todbot/LinkM/c_host/linkm-lib.h

/**
 * linkm-lib --
 *
 * 2009, Tod E. Kurt, ThingM, http://thingm.com/
 *
 */

#ifndef __LINKM_LIB_H_INCLUDED__
#define __LINKM_LIB_H_INCLUDED__

#include <stdint.h>
#include "hiddata.h"

// NOTE: these values much be the same as those in
//       "linkm/firmware/usbconfig.h"           and
//       "linkm/bootloadHID/firmware/usbconfig.h"
//#define IDENT_VENDOR_NUM        0x16C0
//#define IDENT_PRODUCT_NUM       0x05DF
#define IDENT_VENDOR_NUM        0x20A0
#define IDENT_PRODUCT_NUM       0x4110
#define IDENT_VENDOR_STRING     "ThingM"
#define IDENT_PRODUCT_STRING    "LinkM"

// gotta be one more than the size, for the reportid
#define REPORT1_SIZE        17
//#define REPORT1_SIZE        16
#define START_BYTE          0xDA

// Command byte values for linkm_command()
enum {
    LINKM_CMD_NONE     = 0,      // no command, do not use
    // I2C commands
    LINKM_CMD_I2CTRANS = 1,      // i2c read & write (N args: addr + other)
    LINKM_CMD_I2CWRITE = 2,      // i2c write to dev (N args: addr + other)
    LINKM_CMD_I2CREAD  = 3,      // i2c read         (1 args: addr)
    LINKM_CMD_I2CSCAN  = 4,      // i2c bus scan     (2 args: start,end)
    LINKM_CMD_I2CCONN  = 5,      // i2c connect/disc (1 args: 1/0)
    LINKM_CMD_I2CINIT  = 6,      // i2c init         (0 args: )

    // linkm board commands
    LINKM_CMD_VERSIONGET = 100,  // return linkm version
    LINKM_CMD_STATLEDSET = 101,  // status LED set   (1 args: 1/0)
    LINKM_CMD_STATLEDGET = 102,  // status LED get   (0 args)
    LINKM_CMD_PLAYSET    = 103,  // set params of player state machine
    LINKM_CMD_PLAYGET    = 104,  // get params of  player state machine
    LINKM_CMD_EESAVE     = 105,  // save linkm state to EEPROM
    LINKM_CMD_EELOAD     = 106,  // load linkm state from EEPROM
    LINKM_CMD_GOBOOTLOAD = 107,  // trigger USB bootload
};

// Return values for linkm_command()
enum {
    LINKM_ERR_NONE     =   0,
    LINKM_ERR_BADSTART = 101,
    LINKM_ERR_BADARGS,
    LINKM_ERR_I2C,
    LINKM_ERR_I2CREAD,
    LINKM_ERR_NOTOPEN = 199,
};


extern int linkm_debug;


typedef struct {
    uint8_t duration;
    uint8_t cmd;
    uint8_t arg0;
    uint8_t arg1;
    uint8_t arg2;
} scriptline_t;


// public api
int linkm_open(usbDevice_t** dev);
void linkm_close(usbDevice_t* dev);
int linkm_command(usbDevice_t* dev,
                  int cmd,
                  int bytes_send,
                  int bytes_recv,
                  uint8_t* buf_send,
                  uint8_t* buf_recv);
char* linkm_error_msg(int errCode);

// utility
void hexdump(const char* intro, uint8_t* buffer, int len);
int  hexread(uint8_t* buffer, char* string, int buflen);
void linkm_sleep(uint32_t millis);
int parse_scriptlines( char* filename,  scriptline_t* lines );



#endif //__LINKM_LIB_H_INCLUDED__
