todbot/LinkM/c_host/hidsdi.h

/* Name: hidsdi.h
 * Author: Christian Starkjohann
 * Creation Date: 2006-02-02
 * Tabsize: 4
 * Copyright: (c) 2006-2008 by OBJECTIVE DEVELOPMENT Software GmbH
 * License: GNU GPL v2 (see License.txt), GNU GPL v3 or proprietary (CommercialLicense.txt)
 */

/*
General Description
This file is a replacement for hidsdi.h from the Windows DDK. It defines some
of the types and function prototypes of this header for our project. If you
have the Windows DDK version of this file or a version shipped with MinGW, use
that instead.
*/

#ifndef _HIDSDI_H
#define _HIDSDI_H

#include <pshpack4.h>

//#include <ddk/hidusage.h>
//#include <ddk/hidpi.h>

typedef struct{
    ULONG   Size;
    USHORT  VendorID;
    USHORT  ProductID;
    USHORT  VersionNumber;
}HIDD_ATTRIBUTES;

void __stdcall      HidD_GetHidGuid(OUT LPGUID hidGuid);

BOOLEAN __stdcall   HidD_GetAttributes(IN HANDLE device, OUT HIDD_ATTRIBUTES *attributes);

BOOLEAN __stdcall   HidD_GetManufacturerString(IN HANDLE device, OUT void *buffer, IN ULONG bufferLen);
BOOLEAN __stdcall   HidD_GetProductString(IN HANDLE device, OUT void *buffer, IN ULONG bufferLen);
BOOLEAN __stdcall   HidD_GetSerialNumberString(IN HANDLE device, OUT void *buffer, IN ULONG bufferLen);

BOOLEAN __stdcall   HidD_GetFeature(IN HANDLE device, OUT void *reportBuffer, IN ULONG bufferLen);
BOOLEAN __stdcall   HidD_SetFeature(IN HANDLE device, IN void *reportBuffer, IN ULONG bufferLen);

BOOLEAN __stdcall   HidD_GetNumInputBuffers(IN HANDLE device, OUT ULONG *numBuffers);
BOOLEAN __stdcall   HidD_SetNumInputBuffers(IN HANDLE device, OUT ULONG numBuffers);

#include <poppack.h>

#endif
