todbot/LinkM/tools/visual_studio/winddk.h

/*
 * winddk.h
 *
 * Windows Device Driver Kit
 *
 * This file is part of the w32api package.
 *
 * Contributors:
 *   Created by Casper S. Hornstrup <chorns@users.sourceforge.net>
 *
 * THIS SOFTWARE IS NOT COPYRIGHTED
 *
 * This source code is offered for use in the public domain. You may
 * use, modify or distribute it freely.
 *
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
 */

#ifndef __WINDDK_H
#define __WINDDK_H

#define _ANONYMOUS_UNION 
#define _ANONYMOUS_STRUCT

#if __GNUC__ >= 3
#pragma GCC system_header
#endif

#ifdef __cplusplus
extern "C" {
#endif

/*
** Definitions specific to this Device Driver Kit
*/
#define DDKAPI __stdcall
#define DDKFASTAPI __fastcall
#define DDKCDECLAPI __cdecl

#if defined(_NTOSKRNL_)
#ifndef NTOSAPI
#define NTOSAPI DECL_EXPORT
#endif
#define DECLARE_INTERNAL_OBJECT(x) typedef struct _##x; typedef struct _##x *P##x;
#define DECLARE_INTERNAL_OBJECT2(x,y) typedef struct _##x; typedef struct _##x *P##y;
#else
#ifndef NTOSAPI
#define NTOSAPI DECL_IMPORT
#endif
#define DECLARE_INTERNAL_OBJECT(x) struct _##x; typedef struct _##x *P##x;
#define DECLARE_INTERNAL_OBJECT2(x,y) struct _##x; typedef struct _##x *P##y;
#endif

/* Pseudo modifiers for parameters 
   We don't use these unnecessary defines in the w32api headers. Define
   them by default since that is what people expect, but allow users
   to avoid the pollution.  */
#ifndef _NO_W32_PSEUDO_MODIFIERS
#define IN
#define OUT
#define OPTIONAL
#define UNALLIGNED
#endif

#define CONST const
#define VOLATILE volatile

#define RESTRICTED_POINTER
#define POINTER_ALIGNMENT

#ifdef NONAMELESSUNION
# define _DDK_DUMMYUNION_MEMBER(name) DUMMYUNIONNAME.name
# define _DDK_DUMMYUNION_N_MEMBER(n, name) DUMMYUNIONNAME##n.name
#else
# define _DDK_DUMMYUNION_MEMBER(name) name
# define _DDK_DUMMYUNION_N_MEMBER(n, name) name
#endif

/*
** Forward declarations
*/

struct _IRP;
struct _MDL;
struct _KAPC;
struct _KDPC;
struct _KPCR;
struct _KPRCB;
struct _KTSS;
struct _FILE_OBJECT;
struct _DMA_ADAPTER;
struct _DEVICE_OBJECT;
struct _DRIVER_OBJECT;
struct _SECTION_OBJECT;
struct _IO_STATUS_BLOCK;
struct _DEVICE_DESCRIPTION;
struct _SCATTER_GATHER_LIST;

DECLARE_INTERNAL_OBJECT(ADAPTER_OBJECT)
DECLARE_INTERNAL_OBJECT(DMA_ADAPTER)
DECLARE_INTERNAL_OBJECT(IO_STATUS_BLOCK)
DECLARE_INTERNAL_OBJECT(SECTION_OBJECT)

#if 1
/* FIXME: Unknown definitions */
struct _SET_PARTITION_INFORMATION_EX;
typedef ULONG WAIT_TYPE;
typedef HANDLE TRACEHANDLE;
typedef PVOID PWMILIB_CONTEXT;
typedef PVOID PSYSCTL_IRP_DISPOSITION;
typedef ULONG LOGICAL;
#endif

/*
** Routines specific to this DDK
*/

#define TAG(_a, _b, _c, _d) (ULONG) \
	(((_a) << 0) + ((_b) << 8) + ((_c) << 16) + ((_d) << 24))

#ifdef __GNUC__
static __inline struct _KPCR * KeGetCurrentKPCR(
  VOID)
{
  ULONG Value;

  __asm__ __volatile__ (
#if (__GNUC__ >= 3)
    /* support -masm=intel */
    "mov{l} {%%fs:0x18, %0|%0, %%fs:0x18}\n\t"
#else
    "movl %%fs:0x18, %0\n\t"
#endif
     : "=r" (Value)
     : /* no inputs */
  );
  return (struct _KPCR *) Value;
}

#elif defined( __WATCOMC__ )

extern struct _KPCR * KeGetCurrentKPCR( void );
#pragma aux KeGetCurrentKPCR = \
  "mov eax, fs:[0x18]" \
  value [ eax ];

#endif

/*
** Simple structures
*/

typedef LONG KPRIORITY;
typedef UCHAR KIRQL, *PKIRQL;
typedef ULONG_PTR KSPIN_LOCK, *PKSPIN_LOCK;
typedef ULONG_PTR KAFFINITY, *PKAFFINITY;
typedef CCHAR KPROCESSOR_MODE;

typedef enum _MODE {
  KernelMode,
  UserMode,
  MaximumMode
} MODE;


/* Structures not exposed to drivers */
typedef struct _IO_TIMER *PIO_TIMER;
typedef struct _EPROCESS *PEPROCESS;
typedef struct _ETHREAD *PETHREAD;
typedef struct _KINTERRUPT *PKINTERRUPT;
typedef struct _OBJECT_TYPE *POBJECT_TYPE;
typedef struct _KTHREAD *PKTHREAD, *PRKTHREAD;
typedef struct _COMPRESSED_DATA_INFO *PCOMPRESSED_DATA_INFO;
typedef struct _HAL_DISPATCH_TABLE *PHAL_DISPATCH_TABLE;
typedef struct _HAL_PRIVATE_DISPATCH_TABLE *PHAL_PRIVATE_DISPATCH_TABLE;
typedef struct _DRIVE_LAYOUT_INFORMATION *PDRIVE_LAYOUT_INFORMATION;
typedef struct _DRIVE_LAYOUT_INFORMATION_EX *PDRIVE_LAYOUT_INFORMATION_EX;

/* Constants */
#define	MAXIMUM_PROCESSORS                32

#define MAXIMUM_WAIT_OBJECTS              64

#define METHOD_BUFFERED                   0
#define METHOD_IN_DIRECT                  1
#define METHOD_OUT_DIRECT                 2
#define METHOD_NEITHER                    3

#define LOW_PRIORITY                      0
#define LOW_REALTIME_PRIORITY             16
#define HIGH_PRIORITY                     31
#define MAXIMUM_PRIORITY                  32

#define FILE_SUPERSEDED                   0x00000000
#define FILE_OPENED                       0x00000001
#define FILE_CREATED                      0x00000002
#define FILE_OVERWRITTEN                  0x00000003
#define FILE_EXISTS                       0x00000004
#define FILE_DOES_NOT_EXIST               0x00000005

/* also in winnt.h */
//#define FILE_LIST_DIRECTORY               0x00000001
//#define FILE_READ_DATA                    0x00000001
//#define FILE_ADD_FILE                     0x00000002
//#define FILE_WRITE_DATA                   0x00000002
//#define FILE_ADD_SUBDIRECTORY             0x00000004
//#define FILE_APPEND_DATA                  0x00000004
//#define FILE_CREATE_PIPE_INSTANCE         0x00000004
//#define FILE_READ_EA                      0x00000008
//#define FILE_WRITE_EA                     0x00000010
//#define FILE_EXECUTE                      0x00000020
//#define FILE_TRAVERSE                     0x00000020
//#define FILE_DELETE_CHILD                 0x00000040
//#define FILE_READ_ATTRIBUTES              0x00000080
//#define FILE_WRITE_ATTRIBUTES             0x00000100

#define FILE_SHARE_READ                   0x00000001
#define FILE_SHARE_WRITE                  0x00000002
#define FILE_SHARE_DELETE                 0x00000004
#define FILE_SHARE_VALID_FLAGS            0x00000007

#define FILE_ATTRIBUTE_READONLY           0x00000001
#define FILE_ATTRIBUTE_HIDDEN             0x00000002
#define FILE_ATTRIBUTE_SYSTEM             0x00000004
#define FILE_ATTRIBUTE_DIRECTORY          0x00000010
#define FILE_ATTRIBUTE_ARCHIVE            0x00000020
#define FILE_ATTRIBUTE_DEVICE             0x00000040
#define FILE_ATTRIBUTE_NORMAL             0x00000080
#define FILE_ATTRIBUTE_TEMPORARY          0x00000100
#define FILE_ATTRIBUTE_SPARSE_FILE        0x00000200
#define FILE_ATTRIBUTE_REPARSE_POINT      0x00000400
#define FILE_ATTRIBUTE_COMPRESSED         0x00000800
#define FILE_ATTRIBUTE_OFFLINE            0x00001000
#define FILE_ATTRIBUTE_NOT_CONTENT_INDEXED 0x00002000
#define FILE_ATTRIBUTE_ENCRYPTED          0x00004000

#define FILE_ATTRIBUTE_VALID_FLAGS        0x00007fb7
#define FILE_ATTRIBUTE_VALID_SET_FLAGS    0x000031a7

#define FILE_COPY_STRUCTURED_STORAGE      0x00000041
#define FILE_STRUCTURED_STORAGE           0x00000441

#define FILE_VALID_OPTION_FLAGS           0x00ffffff
#define FILE_VALID_PIPE_OPTION_FLAGS      0x00000032
#define FILE_VALID_MAILSLOT_OPTION_FLAGS  0x00000032
#define FILE_VALID_SET_FLAGS              0x00000036

#define FILE_SUPERSEDE                    0x00000000
#define FILE_OPEN                         0x00000001
#define FILE_CREATE                       0x00000002
#define FILE_OPEN_IF                      0x00000003
#define FILE_OVERWRITE                    0x00000004
#define FILE_OVERWRITE_IF                 0x00000005
#define FILE_MAXIMUM_DISPOSITION          0x00000005

#define FILE_DIRECTORY_FILE               0x00000001
#define FILE_WRITE_THROUGH                0x00000002
#define FILE_SEQUENTIAL_ONLY              0x00000004
#define FILE_NO_INTERMEDIATE_BUFFERING    0x00000008
#define FILE_SYNCHRONOUS_IO_ALERT         0x00000010
#define FILE_SYNCHRONOUS_IO_NONALERT      0x00000020
#define FILE_NON_DIRECTORY_FILE           0x00000040
#define FILE_CREATE_TREE_CONNECTION       0x00000080
#define FILE_COMPLETE_IF_OPLOCKED         0x00000100
#define FILE_NO_EA_KNOWLEDGE              0x00000200
#define FILE_OPEN_FOR_RECOVERY            0x00000400
#define FILE_RANDOM_ACCESS                0x00000800
#define FILE_DELETE_ON_CLOSE              0x00001000
#define FILE_OPEN_BY_FILE_ID              0x00002000
#define FILE_OPEN_FOR_BACKUP_INTENT       0x00004000
#define FILE_NO_COMPRESSION               0x00008000
#define FILE_RESERVE_OPFILTER             0x00100000
#define FILE_OPEN_REPARSE_POINT           0x00200000
#define FILE_OPEN_NO_RECALL               0x00400000
#define FILE_OPEN_FOR_FREE_SPACE_QUERY    0x00800000

//#define FILE_ANY_ACCESS                   0x00000000
//#define FILE_SPECIAL_ACCESS               FILE_ANY_ACCESS
//#define FILE_READ_ACCESS                  0x00000001
//#define FILE_WRITE_ACCESS                 0x00000002

#define FILE_ALL_ACCESS \
  (STANDARD_RIGHTS_REQUIRED | \
   SYNCHRONIZE | \
   0x1FF)

#define FILE_GENERIC_EXECUTE \
  (STANDARD_RIGHTS_EXECUTE | \
   FILE_READ_ATTRIBUTES | \
   FILE_EXECUTE | \
   SYNCHRONIZE)

#define FILE_GENERIC_READ \
  (STANDARD_RIGHTS_READ | \
   FILE_READ_DATA | \
   FILE_READ_ATTRIBUTES | \
   FILE_READ_EA | \
   SYNCHRONIZE)

#define FILE_GENERIC_WRITE \
  (STANDARD_RIGHTS_WRITE | \
   FILE_WRITE_DATA | \
   FILE_WRITE_ATTRIBUTES | \
   FILE_WRITE_EA | \
   FILE_APPEND_DATA | \
   SYNCHRONIZE)
/* end winnt.h */

#define DIRECTORY_QUERY (0x0001)
#define DIRECTORY_TRAVERSE (0x0002)
#define DIRECTORY_CREATE_OBJECT (0x0004)
#define DIRECTORY_CREATE_SUBDIRECTORY (0x0008)
#define DIRECTORY_ALL_ACCESS (STANDARD_RIGHTS_REQUIRED | 0xF)
  
/* Exported object types */
extern NTOSAPI POBJECT_TYPE ExDesktopObjectType;
extern NTOSAPI POBJECT_TYPE ExEventObjectType;
extern NTOSAPI POBJECT_TYPE ExSemaphoreObjectType;
extern NTOSAPI POBJECT_TYPE ExWindowStationObjectType;
extern NTOSAPI POBJECT_TYPE IoAdapterObjectType;
extern NTOSAPI ULONG IoDeviceHandlerObjectSize;
extern NTOSAPI POBJECT_TYPE IoDeviceHandlerObjectType;
extern NTOSAPI POBJECT_TYPE IoDeviceObjectType;
extern NTOSAPI POBJECT_TYPE IoDriverObjectType;
extern NTOSAPI POBJECT_TYPE IoFileObjectType;
extern NTOSAPI POBJECT_TYPE LpcPortObjectType;
extern NTOSAPI POBJECT_TYPE MmSectionObjectType;
extern NTOSAPI POBJECT_TYPE SeTokenObjectType;

extern NTOSAPI CCHAR KeNumberProcessors;
extern NTOSAPI PHAL_DISPATCH_TABLE HalDispatchTable;
extern NTOSAPI PHAL_PRIVATE_DISPATCH_TABLE HalPrivateDispatchTable;


/*
** IRP function codes
*/

#define IRP_MJ_CREATE                     0x00
#define IRP_MJ_CREATE_NAMED_PIPE          0x01
#define IRP_MJ_CLOSE                      0x02
#define IRP_MJ_READ                       0x03
#define IRP_MJ_WRITE                      0x04
#define IRP_MJ_QUERY_INFORMATION          0x05
#define IRP_MJ_SET_INFORMATION            0x06
#define IRP_MJ_QUERY_EA                   0x07
#define IRP_MJ_SET_EA                     0x08
#define IRP_MJ_FLUSH_BUFFERS              0x09
#define IRP_MJ_QUERY_VOLUME_INFORMATION   0x0a
#define IRP_MJ_SET_VOLUME_INFORMATION     0x0b
#define IRP_MJ_DIRECTORY_CONTROL          0x0c
#define IRP_MJ_FILE_SYSTEM_CONTROL        0x0d
#define IRP_MJ_DEVICE_CONTROL             0x0e
#define IRP_MJ_INTERNAL_DEVICE_CONTROL    0x0f
#define IRP_MJ_SCSI                       0x0f
#define IRP_MJ_SHUTDOWN                   0x10
#define IRP_MJ_LOCK_CONTROL               0x11
#define IRP_MJ_CLEANUP                    0x12
#define IRP_MJ_CREATE_MAILSLOT            0x13
#define IRP_MJ_QUERY_SECURITY             0x14
#define IRP_MJ_SET_SECURITY               0x15
#define IRP_MJ_POWER                      0x16
#define IRP_MJ_SYSTEM_CONTROL             0x17
#define IRP_MJ_DEVICE_CHANGE              0x18
#define IRP_MJ_QUERY_QUOTA                0x19
#define IRP_MJ_SET_QUOTA                  0x1a
#define IRP_MJ_PNP                        0x1b
#define IRP_MJ_PNP_POWER                  0x1b
#define IRP_MJ_MAXIMUM_FUNCTION           0x1b

#define IRP_MN_QUERY_DIRECTORY            0x01
#define IRP_MN_NOTIFY_CHANGE_DIRECTORY    0x02

#define IRP_MN_USER_FS_REQUEST            0x00
#define IRP_MN_MOUNT_VOLUME               0x01
#define IRP_MN_VERIFY_VOLUME              0x02
#define IRP_MN_LOAD_FILE_SYSTEM           0x03
#define IRP_MN_TRACK_LINK                 0x04
#define IRP_MN_KERNEL_CALL                0x04

#define IRP_MN_LOCK                       0x01
#define IRP_MN_UNLOCK_SINGLE              0x02
#define IRP_MN_UNLOCK_ALL                 0x03
#define IRP_MN_UNLOCK_ALL_BY_KEY          0x04

#define IRP_MN_NORMAL                     0x00
#define IRP_MN_DPC                        0x01
#define IRP_MN_MDL                        0x02
#define IRP_MN_COMPLETE                   0x04
#define IRP_MN_COMPRESSED                 0x08

#define IRP_MN_MDL_DPC                    (IRP_MN_MDL | IRP_MN_DPC)
#define IRP_MN_COMPLETE_MDL               (IRP_MN_COMPLETE | IRP_MN_MDL)
#define IRP_MN_COMPLETE_MDL_DPC           (IRP_MN_COMPLETE_MDL | IRP_MN_DPC)

#define IRP_MN_SCSI_CLASS                 0x01

#define IRP_MN_START_DEVICE               0x00
#define IRP_MN_QUERY_REMOVE_DEVICE        0x01
#define IRP_MN_REMOVE_DEVICE              0x02
#define IRP_MN_CANCEL_REMOVE_DEVICE       0x03
#define IRP_MN_STOP_DEVICE                0x04
#define IRP_MN_QUERY_STOP_DEVICE          0x05
#define IRP_MN_CANCEL_STOP_DEVICE         0x06

#define IRP_MN_QUERY_DEVICE_RELATIONS       0x07
#define IRP_MN_QUERY_INTERFACE              0x08
#define IRP_MN_QUERY_CAPABILITIES           0x09
#define IRP_MN_QUERY_RESOURCES              0x0A
#define IRP_MN_QUERY_RESOURCE_REQUIREMENTS  0x0B
#define IRP_MN_QUERY_DEVICE_TEXT            0x0C
#define IRP_MN_FILTER_RESOURCE_REQUIREMENTS 0x0D

#define IRP_MN_READ_CONFIG                  0x0F
#define IRP_MN_WRITE_CONFIG                 0x10
#define IRP_MN_EJECT                        0x11
#define IRP_MN_SET_LOCK                     0x12
#define IRP_MN_QUERY_ID                     0x13
#define IRP_MN_QUERY_PNP_DEVICE_STATE       0x14
#define IRP_MN_QUERY_BUS_INFORMATION        0x15
#define IRP_MN_DEVICE_USAGE_NOTIFICATION    0x16
#define IRP_MN_SURPRISE_REMOVAL             0x17
#define IRP_MN_QUERY_LEGACY_BUS_INFORMATION 0x18

#define IRP_MN_WAIT_WAKE                  0x00
#define IRP_MN_POWER_SEQUENCE             0x01
#define IRP_MN_SET_POWER                  0x02
#define IRP_MN_QUERY_POWER                0x03

#define IRP_MN_QUERY_ALL_DATA             0x00
#define IRP_MN_QUERY_SINGLE_INSTANCE      0x01
#define IRP_MN_CHANGE_SINGLE_INSTANCE     0x02
#define IRP_MN_CHANGE_SINGLE_ITEM         0x03
#define IRP_MN_ENABLE_EVENTS              0x04
#define IRP_MN_DISABLE_EVENTS             0x05
#define IRP_MN_ENABLE_COLLECTION          0x06
#define IRP_MN_DISABLE_COLLECTION         0x07
#define IRP_MN_REGINFO                    0x08
#define IRP_MN_EXECUTE_METHOD             0x09

#define IRP_MN_REGINFO_EX                 0x0b

typedef enum _IO_ALLOCATION_ACTION {
  KeepObject = 1,
  DeallocateObject,
  DeallocateObjectKeepRegisters
} IO_ALLOCATION_ACTION, *PIO_ALLOCATION_ACTION;

typedef IO_ALLOCATION_ACTION
(DDKAPI *PDRIVER_CONTROL)(
  /*IN*/ struct _DEVICE_OBJECT  *DeviceObject,
  /*IN*/ struct _IRP  *Irp,
  /*IN*/ PVOID  MapRegisterBase,
  /*IN*/ PVOID  Context);

typedef VOID
(DDKAPI *PDRIVER_LIST_CONTROL)(
  /*IN*/ struct _DEVICE_OBJECT  *DeviceObject,
  /*IN*/ struct _IRP  *Irp,
  /*IN*/ struct _SCATTER_GATHER_LIST  *ScatterGather,
  /*IN*/ PVOID  Context);

typedef NTSTATUS
(DDKAPI *PDRIVER_ADD_DEVICE)(
  /*IN*/ struct _DRIVER_OBJECT  *DriverObject,
  /*IN*/ struct _DEVICE_OBJECT  *PhysicalDeviceObject);

typedef NTSTATUS
(DDKAPI *PIO_COMPLETION_ROUTINE)(
  /*IN*/ struct _DEVICE_OBJECT  *DeviceObject,
  /*IN*/ struct _IRP  *Irp,
  /*IN*/ PVOID  Context);

typedef VOID
(DDKAPI *PDRIVER_CANCEL)(
  /*IN*/ struct _DEVICE_OBJECT  *DeviceObject,
  /*IN*/ struct _IRP  *Irp);

typedef VOID
(DDKAPI *PKDEFERRED_ROUTINE)(
  /*IN*/ struct _KDPC  *Dpc,
  /*IN*/ PVOID  DeferredContext,
  /*IN*/ PVOID  SystemArgument1,
  /*IN*/ PVOID  SystemArgument2);

typedef NTSTATUS
(DDKAPI *PDRIVER_DISPATCH)(
  /*IN*/ struct _DEVICE_OBJECT  *DeviceObject,
  /*IN*/ struct _IRP  *Irp);

typedef VOID
(DDKAPI *PIO_DPC_ROUTINE)(
  /*IN*/ struct _KDPC  *Dpc,
  /*IN*/ struct _DEVICE_OBJECT  *DeviceObject,
  /*IN*/ struct _IRP  *Irp,
  /*IN*/ PVOID  Context);

typedef NTSTATUS
(DDKAPI *PMM_DLL_INITIALIZE)(
  /*IN*/ PUNICODE_STRING  RegistryPath);

typedef NTSTATUS
(DDKAPI *PMM_DLL_UNLOAD)(
  VOID);

typedef NTSTATUS
(DDKAPI *PDRIVER_ENTRY)( 
  /*IN*/ struct _DRIVER_OBJECT  *DriverObject, 
  /*IN*/ PUNICODE_STRING  RegistryPath); 

typedef NTSTATUS
(DDKAPI *PDRIVER_INITIALIZE)(
  /*IN*/ struct _DRIVER_OBJECT  *DriverObject, 
  /*IN*/ PUNICODE_STRING  RegistryPath);

typedef BOOLEAN
(DDKAPI *PKSERVICE_ROUTINE)(
  /*IN*/ struct _KINTERRUPT  *Interrupt,
  /*IN*/ PVOID  ServiceContext);

typedef VOID
(DDKAPI *PIO_TIMER_ROUTINE)(
  /*IN*/ struct _DEVICE_OBJECT  *DeviceObject,
  /*IN*/ PVOID  Context);

typedef VOID
(DDKAPI *PDRIVER_REINITIALIZE)( 
  /*IN*/ struct _DRIVER_OBJECT  *DriverObject, 
  /*IN*/ PVOID  Context, 
  /*IN*/ ULONG  Count); 

typedef NTSTATUS
(DDKAPI *PDRIVER_STARTIO)(
  /*IN*/ struct _DEVICE_OBJECT  *DeviceObject,
  /*IN*/ struct _IRP  *Irp);

typedef BOOLEAN
(DDKAPI *PKSYNCHRONIZE_ROUTINE)(
  /*IN*/ PVOID  SynchronizeContext);

typedef VOID
(DDKAPI *PDRIVER_UNLOAD)( 
  /*IN*/ struct _DRIVER_OBJECT  *DriverObject); 



/*
** Plug and Play structures
*/

typedef VOID  (DDKAPI *PINTERFACE_REFERENCE)(PVOID  Context);

typedef VOID 
(DDKAPI *PINTERFACE_DEREFERENCE)(
  PVOID Context);

typedef BOOLEAN 
(DDKAPI *PTRANSLATE_BUS_ADDRESS)(
  /*IN*/ PVOID  Context,
  /*IN*/ PHYSICAL_ADDRESS  BusAddress,
  /*IN*/ ULONG  Length,
  /*IN OUT*/ PULONG  AddressSpace,
  /*OUT*/ PPHYSICAL_ADDRESS  TranslatedAddress);

typedef struct _DMA_ADAPTER* 
(DDKAPI *PGET_DMA_ADAPTER)(
  /*IN*/ PVOID  Context,
  /*IN*/ struct _DEVICE_DESCRIPTION  *DeviceDescriptor,
  /*OUT*/ PULONG  NumberOfMapRegisters);

typedef ULONG 
(DDKAPI *PGET_SET_DEVICE_DATA)(
  /*IN*/ PVOID  Context,
  /*IN*/ ULONG  DataType,
  /*IN*/ PVOID  Buffer,
  /*IN*/ ULONG  Offset,
  /*IN*/ ULONG  Length);

typedef union _POWER_STATE {
  SYSTEM_POWER_STATE  SystemState;
  DEVICE_POWER_STATE  DeviceState;
} POWER_STATE, *PPOWER_STATE;

typedef enum _POWER_STATE_TYPE {
  SystemPowerState,
  DevicePowerState
} POWER_STATE_TYPE, *PPOWER_STATE_TYPE;

typedef struct _BUS_INTERFACE_STANDARD {
  USHORT  Size;
  USHORT  Version;
  PVOID  Context;
  PINTERFACE_REFERENCE  InterfaceReference;
  PINTERFACE_DEREFERENCE  InterfaceDereference;
  PTRANSLATE_BUS_ADDRESS  TranslateBusAddress;
  PGET_DMA_ADAPTER  GetDmaAdapter;
  PGET_SET_DEVICE_DATA  SetBusData;
  PGET_SET_DEVICE_DATA  GetBusData;
} BUS_INTERFACE_STANDARD, *PBUS_INTERFACE_STANDARD;

typedef struct _DEVICE_CAPABILITIES {
  USHORT  Size;
  USHORT  Version;
  ULONG  DeviceD1 : 1;
  ULONG  DeviceD2 : 1;
  ULONG  LockSupported : 1;
  ULONG  EjectSupported : 1;
  ULONG  Removable : 1;
  ULONG  DockDevice : 1;
  ULONG  UniqueID : 1;
  ULONG  SilentInstall : 1;
  ULONG  RawDeviceOK : 1;
  ULONG  SurpriseRemovalOK : 1;
  ULONG  WakeFromD0 : 1;
  ULONG  WakeFromD1 : 1;
  ULONG  WakeFromD2 : 1;
  ULONG  WakeFromD3 : 1;
  ULONG  HardwareDisabled : 1;
  ULONG  NonDynamic : 1;
  ULONG  WarmEjectSupported : 1;
  ULONG  NoDisplayInUI : 1;
  ULONG  Reserved : 14;
  ULONG  Address;
  ULONG  UINumber;
  DEVICE_POWER_STATE  DeviceState[PowerSystemMaximum];
  SYSTEM_POWER_STATE  SystemWake;
  DEVICE_POWER_STATE  DeviceWake;
  ULONG  D1Latency;
  ULONG  D2Latency;
  ULONG  D3Latency;
} DEVICE_CAPABILITIES, *PDEVICE_CAPABILITIES;

typedef struct _DEVICE_INTERFACE_CHANGE_NOTIFICATION {
  USHORT  Version;
  USHORT  Size;
  GUID  Event;
  GUID  InterfaceClassGuid;
  PUNICODE_STRING  SymbolicLinkName;
} DEVICE_INTERFACE_CHANGE_NOTIFICATION, *PDEVICE_INTERFACE_CHANGE_NOTIFICATION;

typedef struct _HWPROFILE_CHANGE_NOTIFICATION {
  USHORT  Version;
  USHORT  Size;
  GUID  Event;
} HWPROFILE_CHANGE_NOTIFICATION, *PHWPROFILE_CHANGE_NOTIFICATION;

#undef INTERFACE

typedef struct _INTERFACE {
  USHORT  Size;
  USHORT  Version;
  PVOID  Context;
  PINTERFACE_REFERENCE  InterfaceReference;
  PINTERFACE_DEREFERENCE  InterfaceDereference;
} INTERFACE, *PINTERFACE; 

typedef struct _PLUGPLAY_NOTIFICATION_HEADER {
  USHORT  Version; 
  USHORT  Size; 
  GUID  Event;
} PLUGPLAY_NOTIFICATION_HEADER, *PPLUGPLAY_NOTIFICATION_HEADER;

typedef ULONG PNP_DEVICE_STATE, *PPNP_DEVICE_STATE;

/* PNP_DEVICE_STATE */

#define PNP_DEVICE_DISABLED                      0x00000001
#define PNP_DEVICE_DONT_DISPLAY_IN_UI            0x00000002
#define PNP_DEVICE_FAILED                        0x00000004
#define PNP_DEVICE_REMOVED                       0x00000008
#define PNP_DEVICE_RESOURCE_REQUIREMENTS_CHANGED 0x00000010
#define PNP_DEVICE_NOT_DISABLEABLE               0x00000020

typedef struct _TARGET_DEVICE_CUSTOM_NOTIFICATION {
  USHORT  Version;
  USHORT  Size;
  GUID  Event;
  struct _FILE_OBJECT  *FileObject;
  LONG  NameBufferOffset;
  UCHAR  CustomDataBuffer[1];
} TARGET_DEVICE_CUSTOM_NOTIFICATION, *PTARGET_DEVICE_CUSTOM_NOTIFICATION;

typedef struct _TARGET_DEVICE_REMOVAL_NOTIFICATION {
  USHORT  Version;
  USHORT  Size;
  GUID  Event;
  struct _FILE_OBJECT  *FileObject;
} TARGET_DEVICE_REMOVAL_NOTIFICATION, *PTARGET_DEVICE_REMOVAL_NOTIFICATION;

typedef enum _BUS_QUERY_ID_TYPE {
  BusQueryDeviceID,
  BusQueryHardwareIDs,
  BusQueryCompatibleIDs,
  BusQueryInstanceID,
  BusQueryDeviceSerialNumber
} BUS_QUERY_ID_TYPE, *PBUS_QUERY_ID_TYPE;

typedef enum _DEVICE_TEXT_TYPE {
  DeviceTextDescription,
  DeviceTextLocationInformation
} DEVICE_TEXT_TYPE, *PDEVICE_TEXT_TYPE;

typedef enum _DEVICE_USAGE_NOTIFICATION_TYPE {
  DeviceUsageTypeUndefined,
  DeviceUsageTypePaging,
  DeviceUsageTypeHibernation,
  DeviceUsageTypeDumpFile
} DEVICE_USAGE_NOTIFICATION_TYPE;

typedef struct _POWER_SEQUENCE {
  ULONG  SequenceD1;
  ULONG  SequenceD2;
  ULONG  SequenceD3;
} POWER_SEQUENCE, *PPOWER_SEQUENCE;

typedef enum {
  DevicePropertyDeviceDescription,
  DevicePropertyHardwareID,
  DevicePropertyCompatibleIDs,
  DevicePropertyBootConfiguration,
  DevicePropertyBootConfigurationTranslated,
  DevicePropertyClassName,
  DevicePropertyClassGuid,
  DevicePropertyDriverKeyName,
  DevicePropertyManufacturer,
  DevicePropertyFriendlyName,
  DevicePropertyLocationInformation,
  DevicePropertyPhysicalDeviceObjectName,
  DevicePropertyBusTypeGuid,
  DevicePropertyLegacyBusType,
  DevicePropertyBusNumber,
  DevicePropertyEnumeratorName,
  DevicePropertyAddress,
  DevicePropertyUINumber,
  DevicePropertyInstallState,
  DevicePropertyRemovalPolicy
} DEVICE_REGISTRY_PROPERTY;

typedef enum _IO_NOTIFICATION_EVENT_CATEGORY {
  EventCategoryReserved,
  EventCategoryHardwareProfileChange,
  EventCategoryDeviceInterfaceChange,
  EventCategoryTargetDeviceChange
} IO_NOTIFICATION_EVENT_CATEGORY;

#define PNPNOTIFY_DEVICE_INTERFACE_INCLUDE_EXISTING_INTERFACES    0x00000001

typedef NTSTATUS 
(DDKAPI *PDRIVER_NOTIFICATION_CALLBACK_ROUTINE)(
  /*IN*/ PVOID NotificationStructure,
  /*IN*/ PVOID Context);

typedef VOID 
(DDKAPI *PDEVICE_CHANGE_COMPLETE_CALLBACK)(
  /*IN*/ PVOID Context);



/*
** System structures
*/

#define SYMBOLIC_LINK_QUERY               0x0001
#define SYMBOLIC_LINK_ALL_ACCESS          (STANDARD_RIGHTS_REQUIRED | 0x1)

/* also in winnt,h */
#define DUPLICATE_CLOSE_SOURCE            0x00000001
#define DUPLICATE_SAME_ACCESS             0x00000002
#define DUPLICATE_SAME_ATTRIBUTES         0x00000004
/* end winnt.h */

typedef struct _OBJECT_NAME_INFORMATION {               
  UNICODE_STRING  Name;                                
} OBJECT_NAME_INFORMATION, *POBJECT_NAME_INFORMATION;   

typedef VOID 
(DDKAPI *PIO_APC_ROUTINE)(
  /*IN*/ PVOID ApcContext,
  /*IN*/ PIO_STATUS_BLOCK IoStatusBlock,
  /*IN*/ ULONG Reserved);

typedef struct _IO_STATUS_BLOCK {
  _ANONYMOUS_UNION union {
    NTSTATUS  Status;
    PVOID  Pointer;
  } DUMMYUNIONNAME;
  ULONG_PTR  Information;
} IO_STATUS_BLOCK;

typedef VOID 
(DDKAPI *PKNORMAL_ROUTINE)(
  /*IN*/ PVOID  NormalContext,
  /*IN*/ PVOID  SystemArgument1,
  /*IN*/ PVOID  SystemArgument2);

typedef VOID 
(DDKAPI *PKKERNEL_ROUTINE)(
  /*IN*/ struct _KAPC  *Apc,
  /*IN OUT*/ PKNORMAL_ROUTINE  *NormalRoutine,
  /*IN OUT*/ PVOID  *NormalContext,
  /*IN OUT*/ PVOID  *SystemArgument1,
  /*IN OUT*/ PVOID  *SystemArgument2);

typedef VOID 
(DDKAPI *PKRUNDOWN_ROUTINE)(
  /*IN*/ struct _KAPC  *Apc);

typedef BOOLEAN 
(DDKAPI *PKTRANSFER_ROUTINE)(
  VOID);

typedef struct _KAPC {
  CSHORT  Type;
  CSHORT  Size;
  ULONG  Spare0;
  struct _KTHREAD  *Thread;
  LIST_ENTRY  ApcListEntry;
  PKKERNEL_ROUTINE  KernelRoutine;
  PKRUNDOWN_ROUTINE  RundownRoutine;
  PKNORMAL_ROUTINE  NormalRoutine;
  PVOID  NormalContext;
  PVOID  SystemArgument1;
  PVOID  SystemArgument2;
  CCHAR  ApcStateIndex;
  KPROCESSOR_MODE  ApcMode;
  BOOLEAN  Inserted;
} KAPC, *PKAPC, *RESTRICTED_POINTER PRKAPC;

typedef struct _KDEVICE_QUEUE {
  CSHORT  Type;
  CSHORT  Size;
  LIST_ENTRY  DeviceListHead;
  KSPIN_LOCK  Lock;
  BOOLEAN  Busy;
} KDEVICE_QUEUE, *PKDEVICE_QUEUE, *RESTRICTED_POINTER PRKDEVICE_QUEUE;

typedef struct _KDEVICE_QUEUE_ENTRY {
  LIST_ENTRY  DeviceListEntry;
  ULONG  SortKey;
  BOOLEAN  Inserted;
} KDEVICE_QUEUE_ENTRY, *PKDEVICE_QUEUE_ENTRY,
*RESTRICTED_POINTER PRKDEVICE_QUEUE_ENTRY;

#define LOCK_QUEUE_WAIT                   1
#define LOCK_QUEUE_OWNER                  2

typedef enum _KSPIN_LOCK_QUEUE_NUMBER {
  LockQueueDispatcherLock,
  LockQueueContextSwapLock,
  LockQueuePfnLock,
  LockQueueSystemSpaceLock,
  LockQueueVacbLock,
  LockQueueMasterLock,
  LockQueueNonPagedPoolLock,
  LockQueueIoCancelLock,
  LockQueueWorkQueueLock,
  LockQueueIoVpbLock,
  LockQueueIoDatabaseLock,
  LockQueueIoCompletionLock,
  LockQueueNtfsStructLock,
  LockQueueAfdWorkQueueLock,
  LockQueueBcbLock,
  LockQueueMaximumLock
} KSPIN_LOCK_QUEUE_NUMBER, *PKSPIN_LOCK_QUEUE_NUMBER;

typedef struct _KSPIN_LOCK_QUEUE {
  struct _KSPIN_LOCK_QUEUE  *VOLATILE Next;
  PKSPIN_LOCK VOLATILE  Lock;
} KSPIN_LOCK_QUEUE, *PKSPIN_LOCK_QUEUE;

typedef struct _KLOCK_QUEUE_HANDLE {
  KSPIN_LOCK_QUEUE  LockQueue;
  KIRQL  OldIrql;
} KLOCK_QUEUE_HANDLE, *PKLOCK_QUEUE_HANDLE;

typedef struct _KDPC {
  CSHORT  Type;
  UCHAR  Number;
  UCHAR  Importance;
  LIST_ENTRY  DpcListEntry;
  PKDEFERRED_ROUTINE  DeferredRoutine;
  PVOID  DeferredContext;
  PVOID  SystemArgument1;
  PVOID  SystemArgument2;
  PULONG_PTR  Lock;
} KDPC, *PKDPC, *RESTRICTED_POINTER PRKDPC;

typedef struct _WAIT_CONTEXT_BLOCK {
  KDEVICE_QUEUE_ENTRY  WaitQueueEntry;
  struct _DRIVER_CONTROL  *DeviceRoutine;
  PVOID  DeviceContext;
  ULONG  NumberOfMapRegisters;
  PVOID  DeviceObject;
  PVOID  CurrentIrp;
  PKDPC  BufferChainingDpc;
} WAIT_CONTEXT_BLOCK, *PWAIT_CONTEXT_BLOCK;

typedef struct _DISPATCHER_HEADER {
  UCHAR  Type;
  UCHAR  Absolute;
  UCHAR  Size;
  UCHAR  Inserted;
  LONG  SignalState;
  LIST_ENTRY  WaitListHead;
} DISPATCHER_HEADER, *PDISPATCHER_HEADER;

typedef struct _KEVENT {
  DISPATCHER_HEADER  Header;
} KEVENT, *PKEVENT, *RESTRICTED_POINTER PRKEVENT;

typedef struct _KSEMAPHORE {
    DISPATCHER_HEADER Header;
    LONG Limit;
} KSEMAPHORE, *PKSEMAPHORE, *RESTRICTED_POINTER PRKSEMAPHORE;

typedef struct _FAST_MUTEX {
  LONG  Count;
  struct _KTHREAD  *Owner;
  ULONG  Contention;
  KEVENT  Event;
  ULONG  OldIrql;
} FAST_MUTEX, *PFAST_MUTEX;

typedef struct _KTIMER {
  DISPATCHER_HEADER  Header;
  ULARGE_INTEGER  DueTime;
  LIST_ENTRY  TimerListEntry;
  struct _KDPC  *Dpc;
  LONG  Period;
} KTIMER, *PKTIMER, *RESTRICTED_POINTER PRKTIMER;

typedef struct _KMUTANT {
  DISPATCHER_HEADER  Header;
  LIST_ENTRY  MutantListEntry;
  struct _KTHREAD  *RESTRICTED_POINTER OwnerThread;
  BOOLEAN  Abandoned;
  UCHAR  ApcDisable;
} KMUTANT, *PKMUTANT, *RESTRICTED_POINTER PRKMUTANT, KMUTEX, *PKMUTEX, *RESTRICTED_POINTER PRKMUTEX;

typedef enum _TIMER_TYPE {
  NotificationTimer,
  SynchronizationTimer
} TIMER_TYPE;

#define EVENT_INCREMENT                   1
#define IO_NO_INCREMENT                   0
#define IO_CD_ROM_INCREMENT               1
#define IO_DISK_INCREMENT                 1
#define IO_KEYBOARD_INCREMENT             6
#define IO_MAILSLOT_INCREMENT             2
#define IO_MOUSE_INCREMENT                6
#define IO_NAMED_PIPE_INCREMENT           2
#define IO_NETWORK_INCREMENT              2
#define IO_PARALLEL_INCREMENT             1
#define IO_SERIAL_INCREMENT               2
#define IO_SOUND_INCREMENT                8
#define IO_VIDEO_INCREMENT                1
#define SEMAPHORE_INCREMENT               1

typedef struct _IRP {
  CSHORT  Type;
  USHORT  Size;
  struct _MDL  *MdlAddress;
  ULONG  Flags;
  union {
    struct _IRP  *MasterIrp;
    LONG  IrpCount;
    PVOID  SystemBuffer;
  } AssociatedIrp;
  LIST_ENTRY  ThreadListEntry;
  IO_STATUS_BLOCK  IoStatus;
  KPROCESSOR_MODE  RequestorMode;
  BOOLEAN  PendingReturned;
  CHAR  StackCount;
  CHAR  CurrentLocation;
  BOOLEAN  Cancel;
  KIRQL  CancelIrql;
  CCHAR  ApcEnvironment;
  UCHAR  AllocationFlags;
  PIO_STATUS_BLOCK  UserIosb;
  PKEVENT  UserEvent;
  union {
    struct {
      PIO_APC_ROUTINE  UserApcRoutine;
      PVOID  UserApcContext;
    } AsynchronousParameters;
    LARGE_INTEGER  AllocationSize;
  } Overlay;
  PDRIVER_CANCEL  CancelRoutine;
  PVOID  UserBuffer;
  union {
    struct {
      _ANONYMOUS_UNION union {
        KDEVICE_QUEUE_ENTRY  DeviceQueueEntry;
        _ANONYMOUS_STRUCT struct {
          PVOID  DriverContext[4];
        } DUMMYSTRUCTNAME;
      } DUMMYUNIONNAME;
      PETHREAD  Thread;
      PCHAR  AuxiliaryBuffer;
      _ANONYMOUS_STRUCT struct {
        LIST_ENTRY  ListEntry;
        _ANONYMOUS_UNION union {
          struct _IO_STACK_LOCATION  *CurrentStackLocation;
          ULONG  PacketType;
        } DUMMYUNIONNAME1;
      } DUMMYSTRUCTNAME1;
      struct _FILE_OBJECT  *OriginalFileObject;
    } Overlay;
    KAPC  Apc;
    PVOID  CompletionKey;
  } Tail;
} IRP;
typedef struct _IRP *PIRP;

/* IRP.Flags */

#define SL_FORCE_ACCESS_CHECK             0x01
#define SL_OPEN_PAGING_FILE               0x02
#define SL_OPEN_TARGET_DIRECTORY          0x04
#define SL_CASE_SENSITIVE                 0x80

#define SL_KEY_SPECIFIED                  0x01
#define SL_OVERRIDE_VERIFY_VOLUME         0x02
#define SL_WRITE_THROUGH                  0x04
#define SL_FT_SEQUENTIAL_WRITE            0x08

#define SL_FAIL_IMMEDIATELY               0x01
#define SL_EXCLUSIVE_LOCK                 0x02

#define SL_RESTART_SCAN                   0x01
#define SL_RETURN_SINGLE_ENTRY            0x02
#define SL_INDEX_SPECIFIED                0x04

#define SL_WATCH_TREE                     0x01

#define SL_ALLOW_RAW_MOUNT                0x01

//#define CTL_CODE(DeviceType, Function, Method, Access)( \
//  ((DeviceType) << 16) | ((Access) << 14) | ((Function) << 2) | (Method))

//#define DEVICE_TYPE_FROM_CTL_CODE(ctl) (((ULONG) (ctl & 0xffff0000)) >> 16)

enum
{
   IRP_NOCACHE = 0x1,
   IRP_PAGING_IO = 0x2,
   IRP_MOUNT_COMPLETION = 0x2,
   IRP_SYNCHRONOUS_API = 0x4,
   IRP_ASSOCIATED_IRP = 0x8,
   IRP_BUFFERED_IO = 0x10,
   IRP_DEALLOCATE_BUFFER = 0x20,
   IRP_INPUT_OPERATION = 0x40,
   IRP_SYNCHRONOUS_PAGING_IO = 0x40,
   IRP_CREATE_OPERATION = 0x80,
   IRP_READ_OPERATION = 0x100,
   IRP_WRITE_OPERATION = 0x200,
   IRP_CLOSE_OPERATION = 0x400,
   IRP_DEFER_IO_COMPLETION = 0x800,
   IRP_OB_QUERY_NAME = 0x1000,
   IRP_HOLD_DEVICE_QUEUE = 0x2000,
   IRP_RETRY_IO_COMPLETION = 0x4000
};

/*
typedef struct  {
  ULONG  Signature;
} DRIVE_LAYOUT_INFORMATION_MBR, *PDRIVE_LAYOUT_INFORMATION_MBR;
typedef struct  {
  GUID  DiskId;
  LARGE_INTEGER  StartingUsableOffset;
  LARGE_INTEGER  UsableLength;
  ULONG  MaxPartitionCount;
} DRIVE_LAYOUT_INFORMATION_GPT, *PDRIVE_LAYOUT_INFORMATION_GPT;

typedef struct _PARTITION_INFORMATION_MBR {
  UCHAR  PartitionType;
  BOOLEAN  BootIndicator;
  BOOLEAN  RecognizedPartition;
  ULONG  HiddenSectors;
} PARTITION_INFORMATION_MBR, *PPARTITION_INFORMATION_MBR;
*/



typedef struct _BOOTDISK_INFORMATION {
  LONGLONG  BootPartitionOffset;
  LONGLONG  SystemPartitionOffset;
  ULONG  BootDeviceSignature;
  ULONG  SystemDeviceSignature;
} BOOTDISK_INFORMATION, *PBOOTDISK_INFORMATION;

typedef struct _BOOTDISK_INFORMATION_EX {
  LONGLONG  BootPartitionOffset;
  LONGLONG  SystemPartitionOffset;
  ULONG  BootDeviceSignature;
  ULONG  SystemDeviceSignature;
  GUID  BootDeviceGuid;
  GUID  SystemDeviceGuid;
  BOOLEAN  BootDeviceIsGpt;
  BOOLEAN  SystemDeviceIsGpt;
} BOOTDISK_INFORMATION_EX, *PBOOTDISK_INFORMATION_EX;

typedef struct _EISA_MEMORY_TYPE {
  UCHAR  ReadWrite : 1;
  UCHAR  Cached : 1;
  UCHAR  Reserved0 : 1;
  UCHAR  Type : 2;
  UCHAR  Shared : 1;
  UCHAR  Reserved1 : 1;
  UCHAR  MoreEntries : 1;
} EISA_MEMORY_TYPE, *PEISA_MEMORY_TYPE;

#include <pshpack1.h>
typedef struct _EISA_MEMORY_CONFIGURATION {
  EISA_MEMORY_TYPE  ConfigurationByte;
  UCHAR  DataSize;
  USHORT  AddressLowWord;
  UCHAR  AddressHighByte;
  USHORT  MemorySize;
} EISA_MEMORY_CONFIGURATION, *PEISA_MEMORY_CONFIGURATION;
#include <poppack.h>

typedef struct _EISA_IRQ_DESCRIPTOR {
  UCHAR  Interrupt : 4;
  UCHAR  Reserved : 1;
  UCHAR  LevelTriggered : 1;
  UCHAR  Shared : 1;
  UCHAR  MoreEntries : 1;
} EISA_IRQ_DESCRIPTOR, *PEISA_IRQ_DESCRIPTOR;

typedef struct _EISA_IRQ_CONFIGURATION {
  EISA_IRQ_DESCRIPTOR  ConfigurationByte;
  UCHAR  Reserved;
} EISA_IRQ_CONFIGURATION, *PEISA_IRQ_CONFIGURATION;

typedef struct _DMA_CONFIGURATION_BYTE0 {
  UCHAR Channel : 3;
  UCHAR Reserved : 3;
  UCHAR Shared : 1;
  UCHAR MoreEntries : 1;
} DMA_CONFIGURATION_BYTE0;

typedef struct _DMA_CONFIGURATION_BYTE1 {
  UCHAR  Reserved0 : 2;
  UCHAR  TransferSize : 2;
  UCHAR  Timing : 2;
  UCHAR  Reserved1 : 2;
} DMA_CONFIGURATION_BYTE1;

typedef struct _EISA_DMA_CONFIGURATION {
  DMA_CONFIGURATION_BYTE0  ConfigurationByte0;
  DMA_CONFIGURATION_BYTE1  ConfigurationByte1;
} EISA_DMA_CONFIGURATION, *PEISA_DMA_CONFIGURATION;

#include <pshpack1.h>
typedef struct _EISA_PORT_DESCRIPTOR {
  UCHAR  NumberPorts : 5;
  UCHAR  Reserved : 1;
  UCHAR  Shared : 1;
  UCHAR  MoreEntries : 1;
} EISA_PORT_DESCRIPTOR, *PEISA_PORT_DESCRIPTOR;

typedef struct _EISA_PORT_CONFIGURATION {
  EISA_PORT_DESCRIPTOR  Configuration;
  USHORT  PortAddress;
} EISA_PORT_CONFIGURATION, *PEISA_PORT_CONFIGURATION;
#include <poppack.h>

typedef struct _CM_EISA_FUNCTION_INFORMATION {
  ULONG  CompressedId;
  UCHAR  IdSlotFlags1;
  UCHAR  IdSlotFlags2;
  UCHAR  MinorRevision;
  UCHAR  MajorRevision;
  UCHAR  Selections[26];
  UCHAR  FunctionFlags;
  UCHAR  TypeString[80];
  EISA_MEMORY_CONFIGURATION  EisaMemory[9];
  EISA_IRQ_CONFIGURATION  EisaIrq[7];
  EISA_DMA_CONFIGURATION  EisaDma[4];
  EISA_PORT_CONFIGURATION  EisaPort[20];
  UCHAR  InitializationData[60];
} CM_EISA_FUNCTION_INFORMATION, *PCM_EISA_FUNCTION_INFORMATION;

/* CM_EISA_FUNCTION_INFORMATION.FunctionFlags */

#define EISA_FUNCTION_ENABLED           0x80
#define EISA_FREE_FORM_DATA             0x40
#define EISA_HAS_PORT_INIT_ENTRY        0x20
#define EISA_HAS_PORT_RANGE             0x10
#define EISA_HAS_DMA_ENTRY              0x08
#define EISA_HAS_IRQ_ENTRY              0x04
#define EISA_HAS_MEMORY_ENTRY           0x02
#define EISA_HAS_TYPE_ENTRY             0x01
#define EISA_HAS_INFORMATION \
  (EISA_HAS_PORT_RANGE + EISA_HAS_DMA_ENTRY + EISA_HAS_IRQ_ENTRY \
  + EISA_HAS_MEMORY_ENTRY + EISA_HAS_TYPE_ENTRY)

typedef struct _CM_EISA_SLOT_INFORMATION {
  UCHAR  ReturnCode;
  UCHAR  ReturnFlags;
  UCHAR  MajorRevision;
  UCHAR  MinorRevision;
  USHORT  Checksum;
  UCHAR  NumberFunctions;
  UCHAR  FunctionInformation;
  ULONG  CompressedId;
} CM_EISA_SLOT_INFORMATION, *PCM_EISA_SLOT_INFORMATION;

/* CM_EISA_SLOT_INFORMATION.ReturnCode */

#define EISA_INVALID_SLOT               0x80
#define EISA_INVALID_FUNCTION           0x81
#define EISA_INVALID_CONFIGURATION      0x82
#define EISA_EMPTY_SLOT                 0x83
#define EISA_INVALID_BIOS_CALL          0x86

typedef struct _CM_FLOPPY_DEVICE_DATA {
  USHORT  Version;
  USHORT  Revision;
  CHAR  Size[8];
  ULONG  MaxDensity;
  ULONG  MountDensity;
  UCHAR  StepRateHeadUnloadTime;
  UCHAR  HeadLoadTime;
  UCHAR  MotorOffTime;
  UCHAR  SectorLengthCode;
  UCHAR  SectorPerTrack;
  UCHAR  ReadWriteGapLength;
  UCHAR  DataTransferLength;
  UCHAR  FormatGapLength;
  UCHAR  FormatFillCharacter;
  UCHAR  HeadSettleTime;
  UCHAR  MotorSettleTime;
  UCHAR  MaximumTrackValue;
  UCHAR  DataTransferRate;
} CM_FLOPPY_DEVICE_DATA, *PCM_FLOPPY_DEVICE_DATA;

typedef enum _INTERFACE_TYPE {
  InterfaceTypeUndefined = -1,
  Internal,
  Isa,
  Eisa,
  MicroChannel,
  TurboChannel,
  PCIBus,
  VMEBus,
  NuBus,
  PCMCIABus,
  CBus,
  MPIBus,
  MPSABus,
  ProcessorInternal,
  InternalPowerBus,
  PNPISABus,
  PNPBus,
  MaximumInterfaceType
} INTERFACE_TYPE, *PINTERFACE_TYPE;

typedef struct _PNP_BUS_INFORMATION {
  GUID  BusTypeGuid;
  INTERFACE_TYPE  LegacyBusType;
  ULONG  BusNumber;
} PNP_BUS_INFORMATION, *PPNP_BUS_INFORMATION;

#include <pshpack1.h>
typedef struct _CM_PARTIAL_RESOURCE_DESCRIPTOR {
  UCHAR Type;
  UCHAR ShareDisposition;
  USHORT Flags;
  union {
    struct {
      PHYSICAL_ADDRESS Start;
      ULONG Length;
    } Generic;
    struct {
      PHYSICAL_ADDRESS Start;
      ULONG Length;
    } Port;
    struct {
      ULONG Level;
      ULONG Vector;
      ULONG Affinity;
    } Interrupt;
    struct {
      PHYSICAL_ADDRESS Start;
      ULONG Length;
    } Memory;
    struct {
      ULONG Channel;
      ULONG Port;
      ULONG Reserved1;
    } Dma;
    struct {
      ULONG Data[3];
    } DevicePrivate;
    struct {
      ULONG Start;
      ULONG Length;
      ULONG Reserved;
    } BusNumber;
    struct {
      ULONG DataSize;
      ULONG Reserved1;
      ULONG Reserved2;
    } DeviceSpecificData;
  } u;
} CM_PARTIAL_RESOURCE_DESCRIPTOR, *PCM_PARTIAL_RESOURCE_DESCRIPTOR;

/* CM_PARTIAL_RESOURCE_DESCRIPTOR.Type */

#define CmResourceTypeNull                0
#define CmResourceTypePort                1
#define CmResourceTypeInterrupt           2
#define CmResourceTypeMemory              3
#define CmResourceTypeDma                 4
#define CmResourceTypeDeviceSpecific      5
#define CmResourceTypeBusNumber           6
#define CmResourceTypeMaximum             7
#define CmResourceTypeNonArbitrated     128
#define CmResourceTypeConfigData        128
#define CmResourceTypeDevicePrivate     129
#define CmResourceTypePcCardConfig      130
#define CmResourceTypeMfCardConfig      131

/* CM_PARTIAL_RESOURCE_DESCRIPTOR.ShareDisposition */

typedef enum _CM_SHARE_DISPOSITION {
  CmResourceShareUndetermined,
  CmResourceShareDeviceExclusive,
  CmResourceShareDriverExclusive,
  CmResourceShareShared
} CM_SHARE_DISPOSITION;

/* CM_PARTIAL_RESOURCE_DESCRIPTOR.Flags if Type = CmResourceTypePort */

#define CM_RESOURCE_PORT_MEMORY           0x0000
#define CM_RESOURCE_PORT_IO               0x0001
#define CM_RESOURCE_PORT_10_BIT_DECODE    0x0004
#define CM_RESOURCE_PORT_12_BIT_DECODE    0x0008
#define CM_RESOURCE_PORT_16_BIT_DECODE    0x0010
#define CM_RESOURCE_PORT_POSITIVE_DECODE  0x0020
#define CM_RESOURCE_PORT_PASSIVE_DECODE   0x0040
#define CM_RESOURCE_PORT_WINDOW_DECODE    0x0080

/* CM_PARTIAL_RESOURCE_DESCRIPTOR.Flags if Type = CmResourceTypeInterrupt */

#define CM_RESOURCE_INTERRUPT_LEVEL_SENSITIVE 0x0000
#define CM_RESOURCE_INTERRUPT_LATCHED         0x0001

/* CM_PARTIAL_RESOURCE_DESCRIPTOR.Flags if Type = CmResourceTypeMemory */

#define CM_RESOURCE_MEMORY_READ_WRITE     0x0000
#define CM_RESOURCE_MEMORY_READ_ONLY      0x0001
#define CM_RESOURCE_MEMORY_WRITE_ONLY     0x0002
#define CM_RESOURCE_MEMORY_PREFETCHABLE   0x0004
#define CM_RESOURCE_MEMORY_COMBINEDWRITE  0x0008
#define CM_RESOURCE_MEMORY_24             0x0010
#define CM_RESOURCE_MEMORY_CACHEABLE      0x0020

/* CM_PARTIAL_RESOURCE_DESCRIPTOR.Flags if Type = CmResourceTypeDma */

#define CM_RESOURCE_DMA_8                 0x0000
#define CM_RESOURCE_DMA_16                0x0001
#define CM_RESOURCE_DMA_32                0x0002
#define CM_RESOURCE_DMA_8_AND_16          0x0004
#define CM_RESOURCE_DMA_BUS_MASTER        0x0008
#define CM_RESOURCE_DMA_TYPE_A            0x0010
#define CM_RESOURCE_DMA_TYPE_B            0x0020
#define CM_RESOURCE_DMA_TYPE_F            0x0040

typedef struct _CM_PARTIAL_RESOURCE_LIST {
  USHORT  Version;
  USHORT  Revision;
  ULONG  Count;
  CM_PARTIAL_RESOURCE_DESCRIPTOR PartialDescriptors[1];
} CM_PARTIAL_RESOURCE_LIST, *PCM_PARTIAL_RESOURCE_LIST;

typedef struct _CM_FULL_RESOURCE_DESCRIPTOR {
  INTERFACE_TYPE  InterfaceType;
  ULONG  BusNumber;
  CM_PARTIAL_RESOURCE_LIST  PartialResourceList;
} CM_FULL_RESOURCE_DESCRIPTOR, *PCM_FULL_RESOURCE_DESCRIPTOR;

typedef struct _CM_RESOURCE_LIST {
  ULONG  Count;
  CM_FULL_RESOURCE_DESCRIPTOR  List[1];
} CM_RESOURCE_LIST, *PCM_RESOURCE_LIST;

typedef struct _CM_INT13_DRIVE_PARAMETER {
  USHORT  DriveSelect;
  ULONG  MaxCylinders;
  USHORT  SectorsPerTrack;
  USHORT  MaxHeads;
  USHORT  NumberDrives;
} CM_INT13_DRIVE_PARAMETER, *PCM_INT13_DRIVE_PARAMETER;
#include <poppack.h>

typedef struct _CM_KEYBOARD_DEVICE_DATA {
  USHORT  Version;
  USHORT  Revision;
  UCHAR  Type;
  UCHAR  Subtype;
  USHORT  KeyboardFlags;
} CM_KEYBOARD_DEVICE_DATA, *PCM_KEYBOARD_DEVICE_DATA;

#define KEYBOARD_INSERT_ON                0x80
#define KEYBOARD_CAPS_LOCK_ON             0x40
#define KEYBOARD_NUM_LOCK_ON              0x20
#define KEYBOARD_SCROLL_LOCK_ON           0x10
#define KEYBOARD_ALT_KEY_DOWN             0x08
#define KEYBOARD_CTRL_KEY_DOWN            0x04
#define KEYBOARD_LEFT_SHIFT_DOWN          0x02
#define KEYBOARD_RIGHT_SHIFT_DOWN         0x01

typedef struct _CM_MCA_POS_DATA {
  USHORT  AdapterId;
  UCHAR  PosData1;
  UCHAR  PosData2;
  UCHAR  PosData3;
  UCHAR  PosData4;
} CM_MCA_POS_DATA, *PCM_MCA_POS_DATA;

/*
typedef struct CM_Power_Data_s {
  ULONG  PD_Size;
  DEVICE_POWER_STATE  PD_MostRecentPowerState;
  ULONG  PD_Capabilities;
  ULONG  PD_D1Latency;
  ULONG  PD_D2Latency;
  ULONG  PD_D3Latency;
  DEVICE_POWER_STATE  PD_PowerStateMapping[PowerSystemMaximum];
} CM_POWER_DATA, *PCM_POWER_DATA;
*/

#define PDCAP_D0_SUPPORTED                0x00000001
#define PDCAP_D1_SUPPORTED                0x00000002
#define PDCAP_D2_SUPPORTED                0x00000004
#define PDCAP_D3_SUPPORTED                0x00000008
#define PDCAP_WAKE_FROM_D0_SUPPORTED      0x00000010
#define PDCAP_WAKE_FROM_D1_SUPPORTED      0x00000020
#define PDCAP_WAKE_FROM_D2_SUPPORTED      0x00000040
#define PDCAP_WAKE_FROM_D3_SUPPORTED      0x00000080
#define PDCAP_WARM_EJECT_SUPPORTED        0x00000100

typedef struct _CM_SCSI_DEVICE_DATA {
  USHORT  Version;
  USHORT  Revision;
  UCHAR  HostIdentifier;
} CM_SCSI_DEVICE_DATA, *PCM_SCSI_DEVICE_DATA;

typedef struct _CM_SERIAL_DEVICE_DATA {
  USHORT  Version;
  USHORT  Revision;
  ULONG  BaudClock;
} CM_SERIAL_DEVICE_DATA, *PCM_SERIAL_DEVICE_DATA;

/* IO_RESOURCE_DESCRIPTOR.Option */

#define IO_RESOURCE_PREFERRED             0x01
#define IO_RESOURCE_DEFAULT               0x02
#define IO_RESOURCE_ALTERNATIVE           0x08

typedef struct _IO_RESOURCE_DESCRIPTOR {
  UCHAR  Option;
  UCHAR  Type;
  UCHAR  ShareDisposition;
  UCHAR  Spare1;
  USHORT  Flags;
  USHORT  Spare2;
  union {
    struct {
      ULONG  Length;
      ULONG  Alignment;
      PHYSICAL_ADDRESS  MinimumAddress;
      PHYSICAL_ADDRESS  MaximumAddress;
    } Port;
    struct {
      ULONG  Length;
      ULONG  Alignment;
      PHYSICAL_ADDRESS  MinimumAddress;
      PHYSICAL_ADDRESS  MaximumAddress;
    } Memory;
    struct {
      ULONG  MinimumVector;
      ULONG  MaximumVector;
    } Interrupt;
    struct {
      ULONG  MinimumChannel;
      ULONG  MaximumChannel;
    } Dma;
    struct {
      ULONG  Length;
      ULONG  Alignment;
      PHYSICAL_ADDRESS  MinimumAddress;
      PHYSICAL_ADDRESS  MaximumAddress;
    } Generic;
    struct {
      ULONG  Data[3];
    } DevicePrivate;
    struct {
      ULONG  Length;
      ULONG  MinBusNumber;
      ULONG  MaxBusNumber;
      ULONG  Reserved;
    } BusNumber;
    struct {
      ULONG  Priority;
      ULONG  Reserved1;
      ULONG  Reserved2;
    } ConfigData;
  } u;
} IO_RESOURCE_DESCRIPTOR, *PIO_RESOURCE_DESCRIPTOR;

typedef struct _IO_RESOURCE_LIST {
  USHORT  Version;
  USHORT  Revision;
  ULONG  Count;
  IO_RESOURCE_DESCRIPTOR  Descriptors[1];
} IO_RESOURCE_LIST, *PIO_RESOURCE_LIST;

typedef struct _IO_RESOURCE_REQUIREMENTS_LIST {
  ULONG  ListSize;
  INTERFACE_TYPE  InterfaceType;
  ULONG  BusNumber;
  ULONG  SlotNumber;
  ULONG  Reserved[3];
  ULONG  AlternativeLists;
  IO_RESOURCE_LIST  List[1];
} IO_RESOURCE_REQUIREMENTS_LIST, *PIO_RESOURCE_REQUIREMENTS_LIST;

typedef struct _CONTROLLER_OBJECT {
  CSHORT  Type;
  CSHORT  Size;
  PVOID  ControllerExtension;
  KDEVICE_QUEUE  DeviceWaitQueue;
  ULONG  Spare1;
  LARGE_INTEGER  Spare2;
} CONTROLLER_OBJECT, *PCONTROLLER_OBJECT;

typedef enum _DMA_WIDTH {
  Width8Bits,
  Width16Bits,
  Width32Bits,
  MaximumDmaWidth
} DMA_WIDTH, *PDMA_WIDTH;

typedef enum _DMA_SPEED {
  Compatible,
  TypeA,
  TypeB,
  TypeC,
  TypeF,
  MaximumDmaSpeed
} DMA_SPEED, *PDMA_SPEED;

/* DEVICE_DESCRIPTION.Version */

#define DEVICE_DESCRIPTION_VERSION        0x0000
#define DEVICE_DESCRIPTION_VERSION1       0x0001
#define DEVICE_DESCRIPTION_VERSION2       0x0002

typedef struct _DEVICE_DESCRIPTION {
  ULONG  Version;
  BOOLEAN  Master;
  BOOLEAN  ScatterGather;
  BOOLEAN  DemandMode;
  BOOLEAN  AutoInitialize;
  BOOLEAN  Dma32BitAddresses;
  BOOLEAN  IgnoreCount;
  BOOLEAN  Reserved1;
  BOOLEAN  Dma64BitAddresses;
  ULONG  BusNumber; 
  ULONG  DmaChannel;
  INTERFACE_TYPE  InterfaceType;
  DMA_WIDTH  DmaWidth;
  DMA_SPEED  DmaSpeed;
  ULONG  MaximumLength;
  ULONG  DmaPort;
} DEVICE_DESCRIPTION, *PDEVICE_DESCRIPTION;

/* VPB.Flags */
#define VPB_MOUNTED                       0x0001
#define VPB_LOCKED                        0x0002
#define VPB_PERSISTENT                    0x0004
#define VPB_REMOVE_PENDING                0x0008
#define VPB_RAW_MOUNT                     0x0010

#define MAXIMUM_VOLUME_LABEL_LENGTH       (32 * sizeof(WCHAR))

typedef struct _VPB {
  CSHORT  Type;
  CSHORT  Size;
  USHORT  Flags;
  USHORT  VolumeLabelLength;
  struct _DEVICE_OBJECT  *DeviceObject;
  struct _DEVICE_OBJECT  *RealDevice;
  ULONG  SerialNumber;
  ULONG  ReferenceCount;
  WCHAR  VolumeLabel[MAXIMUM_VOLUME_LABEL_LENGTH / sizeof(WCHAR)];
} VPB, *PVPB;

/* DEVICE_OBJECT.Flags */

#define DO_VERIFY_VOLUME                  0x00000002      
#define DO_BUFFERED_IO                    0x00000004      
#define DO_EXCLUSIVE                      0x00000008      
#define DO_DIRECT_IO                      0x00000010      
#define DO_MAP_IO_BUFFER                  0x00000020      
#define DO_DEVICE_HAS_NAME                0x00000040      
#define DO_DEVICE_INITIALIZING            0x00000080      
#define DO_SYSTEM_BOOT_PARTITION          0x00000100      
#define DO_LONG_TERM_REQUESTS             0x00000200      
#define DO_NEVER_LAST_DEVICE              0x00000400      
#define DO_SHUTDOWN_REGISTERED            0x00000800      
#define DO_BUS_ENUMERATED_DEVICE          0x00001000      
#define DO_POWER_PAGABLE                  0x00002000      
#define DO_POWER_INRUSH                   0x00004000      
#define DO_LOW_PRIORITY_FILESYSTEM        0x00010000      

/* DEVICE_OBJECT.Characteristics */

#define FILE_REMOVABLE_MEDIA            0x00000001
#define FILE_READ_ONLY_DEVICE           0x00000002
#define FILE_FLOPPY_DISKETTE            0x00000004
#define FILE_WRITE_ONCE_MEDIA           0x00000008
#define FILE_REMOTE_DEVICE              0x00000010
#define FILE_DEVICE_IS_MOUNTED          0x00000020
#define FILE_VIRTUAL_VOLUME             0x00000040
#define FILE_AUTOGENERATED_DEVICE_NAME  0x00000080
#define FILE_DEVICE_SECURE_OPEN         0x00000100

/* DEVICE_OBJECT.AlignmentRequirement */

#define FILE_BYTE_ALIGNMENT             0x00000000
#define FILE_WORD_ALIGNMENT             0x00000001
#define FILE_LONG_ALIGNMENT             0x00000003
#define FILE_QUAD_ALIGNMENT             0x00000007
#define FILE_OCTA_ALIGNMENT             0x0000000f
#define FILE_32_BYTE_ALIGNMENT          0x0000001f
#define FILE_64_BYTE_ALIGNMENT          0x0000003f
#define FILE_128_BYTE_ALIGNMENT         0x0000007f
#define FILE_256_BYTE_ALIGNMENT         0x000000ff
#define FILE_512_BYTE_ALIGNMENT         0x000001ff

/* DEVICE_OBJECT.DeviceType */

//#define DEVICE_TYPE ULONG

#define FILE_DEVICE_BEEP                  0x00000001
#define FILE_DEVICE_CD_ROM                0x00000002
#define FILE_DEVICE_CD_ROM_FILE_SYSTEM    0x00000003
#define FILE_DEVICE_CONTROLLER            0x00000004
#define FILE_DEVICE_DATALINK              0x00000005
#define FILE_DEVICE_DFS                   0x00000006
#define FILE_DEVICE_DISK                  0x00000007
#define FILE_DEVICE_DISK_FILE_SYSTEM      0x00000008
#define FILE_DEVICE_FILE_SYSTEM           0x00000009
#define FILE_DEVICE_INPORT_PORT           0x0000000a
#define FILE_DEVICE_KEYBOARD              0x0000000b
#define FILE_DEVICE_MAILSLOT              0x0000000c
#define FILE_DEVICE_MIDI_IN               0x0000000d
#define FILE_DEVICE_MIDI_OUT              0x0000000e
#define FILE_DEVICE_MOUSE                 0x0000000f
#define FILE_DEVICE_MULTI_UNC_PROVIDER    0x00000010
#define FILE_DEVICE_NAMED_PIPE            0x00000011
#define FILE_DEVICE_NETWORK               0x00000012
#define FILE_DEVICE_NETWORK_BROWSER       0x00000013
#define FILE_DEVICE_NETWORK_FILE_SYSTEM   0x00000014
#define FILE_DEVICE_NULL                  0x00000015
#define FILE_DEVICE_PARALLEL_PORT         0x00000016
#define FILE_DEVICE_PHYSICAL_NETCARD      0x00000017
#define FILE_DEVICE_PRINTER               0x00000018
#define FILE_DEVICE_SCANNER               0x00000019
#define FILE_DEVICE_SERIAL_MOUSE_PORT     0x0000001a
#define FILE_DEVICE_SERIAL_PORT           0x0000001b
#define FILE_DEVICE_SCREEN                0x0000001c
#define FILE_DEVICE_SOUND                 0x0000001d
#define FILE_DEVICE_STREAMS               0x0000001e
#define FILE_DEVICE_TAPE                  0x0000001f
#define FILE_DEVICE_TAPE_FILE_SYSTEM      0x00000020
#define FILE_DEVICE_TRANSPORT             0x00000021
#define FILE_DEVICE_UNKNOWN               0x00000022
#define FILE_DEVICE_VIDEO                 0x00000023
#define FILE_DEVICE_VIRTUAL_DISK          0x00000024
#define FILE_DEVICE_WAVE_IN               0x00000025
#define FILE_DEVICE_WAVE_OUT              0x00000026
#define FILE_DEVICE_8042_PORT             0x00000027
#define FILE_DEVICE_NETWORK_REDIRECTOR    0x00000028
#define FILE_DEVICE_BATTERY               0x00000029
#define FILE_DEVICE_BUS_EXTENDER          0x0000002a
#define FILE_DEVICE_MODEM                 0x0000002b
#define FILE_DEVICE_VDM                   0x0000002c
#define FILE_DEVICE_MASS_STORAGE          0x0000002d
#define FILE_DEVICE_SMB                   0x0000002e
#define FILE_DEVICE_KS                    0x0000002f
#define FILE_DEVICE_CHANGER               0x00000030
#define FILE_DEVICE_SMARTCARD             0x00000031
#define FILE_DEVICE_ACPI                  0x00000032
#define FILE_DEVICE_DVD                   0x00000033
#define FILE_DEVICE_FULLSCREEN_VIDEO      0x00000034
#define FILE_DEVICE_DFS_FILE_SYSTEM       0x00000035
#define FILE_DEVICE_DFS_VOLUME            0x00000036
#define FILE_DEVICE_SERENUM               0x00000037
#define FILE_DEVICE_TERMSRV               0x00000038
#define FILE_DEVICE_KSEC                  0x00000039
//#define FILE_DEVICE_FIPS		              0x0000003a

typedef struct _DEVICE_OBJECT {
  CSHORT  Type;
  USHORT  Size;
  LONG  ReferenceCount;
  struct _DRIVER_OBJECT  *DriverObject;
  struct _DEVICE_OBJECT  *NextDevice;
  struct _DEVICE_OBJECT  *AttachedDevice;
  struct _IRP  *CurrentIrp;
  PIO_TIMER  Timer;
  ULONG  Flags;
  ULONG  Characteristics;
  PVPB  Vpb;
  PVOID  DeviceExtension;
  DEVICE_TYPE  DeviceType;
  CCHAR  StackSize;
  union {
    LIST_ENTRY  ListEntry;
    WAIT_CONTEXT_BLOCK  Wcb;
  } Queue;
  ULONG  AlignmentRequirement;
  KDEVICE_QUEUE  DeviceQueue;
  KDPC  Dpc;
  ULONG  ActiveThreadCount;
  PSECURITY_DESCRIPTOR  SecurityDescriptor;
  KEVENT  DeviceLock;
  USHORT  SectorSize;
  USHORT  Spare1;
  struct _DEVOBJ_EXTENSION  *DeviceObjectExtension;
  PVOID  Reserved;
} DEVICE_OBJECT;
typedef struct _DEVICE_OBJECT *PDEVICE_OBJECT;

typedef enum _DEVICE_RELATION_TYPE {
  BusRelations,
  EjectionRelations,
  PowerRelations,
  RemovalRelations,
  TargetDeviceRelation,
  SingleBusRelations
} DEVICE_RELATION_TYPE, *PDEVICE_RELATION_TYPE;

typedef struct _DEVICE_RELATIONS {
  ULONG  Count;
  PDEVICE_OBJECT Objects[1];
} DEVICE_RELATIONS, *PDEVICE_RELATIONS;

typedef struct _SCATTER_GATHER_ELEMENT {
  PHYSICAL_ADDRESS  Address;   
  ULONG  Length;          
  ULONG_PTR  Reserved;
} SCATTER_GATHER_ELEMENT, *PSCATTER_GATHER_ELEMENT;

typedef struct _SCATTER_GATHER_LIST {
  ULONG  NumberOfElements;
  ULONG_PTR  Reserved;
  SCATTER_GATHER_ELEMENT  Elements[0];
} SCATTER_GATHER_LIST, *PSCATTER_GATHER_LIST;

typedef struct _MDL {
  struct _MDL  *Next;
  CSHORT  Size;
  CSHORT  MdlFlags;
  struct _EPROCESS  *Process;
  PVOID  MappedSystemVa;
  PVOID  StartVa;
  ULONG  ByteCount;
  ULONG  ByteOffset;
} MDL, *PMDL;

#define MDL_MAPPED_TO_SYSTEM_VA           0x0001
#define MDL_PAGES_LOCKED                  0x0002
#define MDL_SOURCE_IS_NONPAGED_POOL       0x0004
#define MDL_ALLOCATED_FIXED_SIZE          0x0008
#define MDL_PARTIAL                       0x0010
#define MDL_PARTIAL_HAS_BEEN_MAPPED       0x0020
#define MDL_IO_PAGE_READ                  0x0040
#define MDL_WRITE_OPERATION               0x0080
#define MDL_PARENT_MAPPED_SYSTEM_VA       0x0100
#define MDL_FREE_EXTRA_PTES               0x0200
#define MDL_IO_SPACE                      0x0800
#define MDL_NETWORK_HEADER                0x1000
#define MDL_MAPPING_CAN_FAIL              0x2000
#define MDL_ALLOCATED_MUST_SUCCEED        0x4000

#define MDL_MAPPING_FLAGS ( \
  MDL_MAPPED_TO_SYSTEM_VA     | \
  MDL_PAGES_LOCKED            | \
  MDL_SOURCE_IS_NONPAGED_POOL | \
  MDL_PARTIAL_HAS_BEEN_MAPPED | \
  MDL_PARENT_MAPPED_SYSTEM_VA | \
  MDL_SYSTEM_VA               | \
  MDL_IO_SPACE)

typedef VOID 
(DDKAPI *PPUT_DMA_ADAPTER)(
  /*IN*/ PDMA_ADAPTER  DmaAdapter);

typedef PVOID 
(DDKAPI *PALLOCATE_COMMON_BUFFER)(
  /*IN*/ PDMA_ADAPTER  DmaAdapter,
  /*IN*/ ULONG  Length,
  /*OUT*/ PPHYSICAL_ADDRESS  LogicalAddress,
  /*IN*/ BOOLEAN  CacheEnabled);

typedef VOID 
(DDKAPI *PFREE_COMMON_BUFFER)(
  /*IN*/ PDMA_ADAPTER  DmaAdapter,
  /*IN*/ ULONG  Length,
  /*IN*/ PHYSICAL_ADDRESS  LogicalAddress,
  /*IN*/ PVOID  VirtualAddress,
  /*IN*/ BOOLEAN  CacheEnabled);

typedef NTSTATUS 
(DDKAPI *PALLOCATE_ADAPTER_CHANNEL)(
  /*IN*/ PDMA_ADAPTER  DmaAdapter,
  /*IN*/ PDEVICE_OBJECT  DeviceObject,
  /*IN*/ ULONG  NumberOfMapRegisters,
  /*IN*/ PDRIVER_CONTROL  ExecutionRoutine,
  /*IN*/ PVOID  Context);

typedef BOOLEAN 
(DDKAPI *PFLUSH_ADAPTER_BUFFERS)(
  /*IN*/ PDMA_ADAPTER  DmaAdapter,
  /*IN*/ PMDL  Mdl,
  /*IN*/ PVOID  MapRegisterBase,
  /*IN*/ PVOID  CurrentVa,
  /*IN*/ ULONG  Length,
  /*IN*/ BOOLEAN  WriteToDevice);

typedef VOID 
(DDKAPI *PFREE_ADAPTER_CHANNEL)(
  /*IN*/ PDMA_ADAPTER  DmaAdapter);

typedef VOID 
(DDKAPI *PFREE_MAP_REGISTERS)(
  /*IN*/ PDMA_ADAPTER  DmaAdapter,
  PVOID  MapRegisterBase,
  ULONG  NumberOfMapRegisters);

typedef PHYSICAL_ADDRESS 
(DDKAPI *PMAP_TRANSFER)(
  /*IN*/ PDMA_ADAPTER  DmaAdapter,
  /*IN*/ PMDL  Mdl,
  /*IN*/ PVOID  MapRegisterBase,
  /*IN*/ PVOID  CurrentVa,
  /*IN OUT*/ PULONG  Length,
  /*IN*/ BOOLEAN  WriteToDevice);

typedef ULONG 
(DDKAPI *PGET_DMA_ALIGNMENT)(
  /*IN*/ PDMA_ADAPTER  DmaAdapter);

typedef ULONG 
(DDKAPI *PREAD_DMA_COUNTER)(
  /*IN*/ PDMA_ADAPTER  DmaAdapter);

typedef NTSTATUS 
(DDKAPI *PGET_SCATTER_GATHER_LIST)(
  /*IN*/ PDMA_ADAPTER  DmaAdapter,
  /*IN*/ PDEVICE_OBJECT  DeviceObject,
  /*IN*/ PMDL  Mdl,
  /*IN*/ PVOID  CurrentVa,
  /*IN*/ ULONG  Length,
  /*IN*/ PDRIVER_LIST_CONTROL  ExecutionRoutine,
  /*IN*/ PVOID  Context,
  /*IN*/ BOOLEAN  WriteToDevice);

typedef VOID 
(DDKAPI *PPUT_SCATTER_GATHER_LIST)(
  /*IN*/ PDMA_ADAPTER  DmaAdapter,
  /*IN*/ PSCATTER_GATHER_LIST  ScatterGather,
  /*IN*/ BOOLEAN  WriteToDevice);

typedef NTSTATUS 
(DDKAPI *PCALCULATE_SCATTER_GATHER_LIST_SIZE)(
  /*IN*/ PDMA_ADAPTER  DmaAdapter,
  /*IN*/ PMDL  Mdl  /*OPTIONAL*/,
  /*IN*/ PVOID  CurrentVa,
  /*IN*/ ULONG  Length,
  /*OUT*/ PULONG  ScatterGatherListSize,
  /*OUT*/ PULONG  pNumberOfMapRegisters  /*OPTIONAL*/);

typedef NTSTATUS 
(DDKAPI *PBUILD_SCATTER_GATHER_LIST)(
  /*IN*/ PDMA_ADAPTER  DmaAdapter,
  /*IN*/ PDEVICE_OBJECT  DeviceObject,
  /*IN*/ PMDL  Mdl,
  /*IN*/ PVOID  CurrentVa,
  /*IN*/ ULONG  Length,
  /*IN*/ PDRIVER_LIST_CONTROL  ExecutionRoutine,
  /*IN*/ PVOID  Context,
  /*IN*/ BOOLEAN  WriteToDevice,
  /*IN*/ PVOID  ScatterGatherBuffer,
  /*IN*/ ULONG  ScatterGatherLength);

typedef NTSTATUS 
(DDKAPI *PBUILD_MDL_FROM_SCATTER_GATHER_LIST)(
  /*IN*/ PDMA_ADAPTER  DmaAdapter,
  /*IN*/ PSCATTER_GATHER_LIST  ScatterGather,
  /*IN*/ PMDL  OriginalMdl,
  /*OUT*/ PMDL  *TargetMdl);

typedef struct _DMA_OPERATIONS {
  ULONG  Size;
  PPUT_DMA_ADAPTER  PutDmaAdapter;
  PALLOCATE_COMMON_BUFFER  AllocateCommonBuffer;
  PFREE_COMMON_BUFFER  FreeCommonBuffer;
  PALLOCATE_ADAPTER_CHANNEL  AllocateAdapterChannel;
  PFLUSH_ADAPTER_BUFFERS  FlushAdapterBuffers;
  PFREE_ADAPTER_CHANNEL  FreeAdapterChannel;
  PFREE_MAP_REGISTERS  FreeMapRegisters;
  PMAP_TRANSFER  MapTransfer;
  PGET_DMA_ALIGNMENT  GetDmaAlignment;
  PREAD_DMA_COUNTER  ReadDmaCounter;
  PGET_SCATTER_GATHER_LIST  GetScatterGatherList;
  PPUT_SCATTER_GATHER_LIST  PutScatterGatherList;
  PCALCULATE_SCATTER_GATHER_LIST_SIZE  CalculateScatterGatherList;
  PBUILD_SCATTER_GATHER_LIST  BuildScatterGatherList;
  PBUILD_MDL_FROM_SCATTER_GATHER_LIST  BuildMdlFromScatterGatherList;
} DMA_OPERATIONS, *PDMA_OPERATIONS;

typedef struct _DMA_ADAPTER {
  USHORT  Version;
  USHORT  Size;
  PDMA_OPERATIONS  DmaOperations;
} DMA_ADAPTER;

typedef enum _FILE_INFORMATION_CLASS {
  FileDirectoryInformation = 1,
  FileFullDirectoryInformation,
  FileBothDirectoryInformation,
  FileBasicInformation,
  FileStandardInformation,
  FileInternalInformation,
  FileEaInformation,
  FileAccessInformation,
  FileNameInformation,
  FileRenameInformation,
  FileLinkInformation,
  FileNamesInformation,
  FileDispositionInformation,
  FilePositionInformation,
  FileFullEaInformation,
  FileModeInformation,
  FileAlignmentInformation,
  FileAllInformation,
  FileAllocationInformation,
  FileEndOfFileInformation,
  FileAlternateNameInformation,
  FileStreamInformation,
  FilePipeInformation,
  FilePipeLocalInformation,
  FilePipeRemoteInformation,
  FileMailslotQueryInformation,
  FileMailslotSetInformation,
  FileCompressionInformation,
  FileObjectIdInformation,
  FileCompletionInformation,
  FileMoveClusterInformation,
  FileQuotaInformation,
  FileReparsePointInformation,
  FileNetworkOpenInformation,
  FileAttributeTagInformation,
  FileTrackingInformation,
  FileIdBothDirectoryInformation,
  FileIdFullDirectoryInformation,
  FileValidDataLengthInformation,
  FileShortNameInformation,
  FileMaximumInformation
} FILE_INFORMATION_CLASS, *PFILE_INFORMATION_CLASS;

typedef struct _FILE_POSITION_INFORMATION {                 
  LARGE_INTEGER  CurrentByteOffset;                        
} FILE_POSITION_INFORMATION, *PFILE_POSITION_INFORMATION;   

typedef struct _FILE_ALIGNMENT_INFORMATION {
  ULONG  AlignmentRequirement;
} FILE_ALIGNMENT_INFORMATION;

typedef struct _FILE_NAME_INFORMATION {                     
  ULONG  FileNameLength;                                   
  WCHAR  FileName[1];                                      
} FILE_NAME_INFORMATION, *PFILE_NAME_INFORMATION;           

typedef struct _FILE_BASIC_INFORMATION {
  LARGE_INTEGER  CreationTime;
  LARGE_INTEGER  LastAccessTime;
  LARGE_INTEGER  LastWriteTime;
  LARGE_INTEGER  ChangeTime;
  ULONG  FileAttributes;
} FILE_BASIC_INFORMATION, *PFILE_BASIC_INFORMATION;

typedef struct _FILE_STANDARD_INFORMATION {
  LARGE_INTEGER  AllocationSize;
  LARGE_INTEGER  EndOfFile;
  ULONG  NumberOfLinks;
  BOOLEAN  DeletePending;
  BOOLEAN  Directory;
} FILE_STANDARD_INFORMATION, *PFILE_STANDARD_INFORMATION;

typedef struct _FILE_NETWORK_OPEN_INFORMATION {                 
  LARGE_INTEGER  CreationTime;                                 
  LARGE_INTEGER  LastAccessTime;                               
  LARGE_INTEGER  LastWriteTime;                                
  LARGE_INTEGER  ChangeTime;                                   
  LARGE_INTEGER  AllocationSize;                               
  LARGE_INTEGER  EndOfFile;                                    
  ULONG  FileAttributes;                                       
} FILE_NETWORK_OPEN_INFORMATION, *PFILE_NETWORK_OPEN_INFORMATION;   

typedef struct _FILE_ATTRIBUTE_TAG_INFORMATION {               
  ULONG  FileAttributes;                                       
  ULONG  ReparseTag;                                           
} FILE_ATTRIBUTE_TAG_INFORMATION, *PFILE_ATTRIBUTE_TAG_INFORMATION;

typedef struct _FILE_DISPOSITION_INFORMATION {                  
  BOOLEAN  DoDeleteFile;                                         
} FILE_DISPOSITION_INFORMATION, *PFILE_DISPOSITION_INFORMATION; 
                                                                
typedef struct _FILE_END_OF_FILE_INFORMATION {                  
  LARGE_INTEGER  EndOfFile;                                    
} FILE_END_OF_FILE_INFORMATION, *PFILE_END_OF_FILE_INFORMATION; 
                                                                
typedef struct _FILE_VALID_DATA_LENGTH_INFORMATION {                                    
  LARGE_INTEGER  ValidDataLength;                                                      
} FILE_VALID_DATA_LENGTH_INFORMATION, *PFILE_VALID_DATA_LENGTH_INFORMATION;             

typedef enum _FSINFOCLASS {
  FileFsVolumeInformation = 1,
  FileFsLabelInformation,
  FileFsSizeInformation,
  FileFsDeviceInformation,
  FileFsAttributeInformation,
  FileFsControlInformation,
  FileFsFullSizeInformation,
  FileFsObjectIdInformation,
  FileFsDriverPathInformation,
  FileFsMaximumInformation
} FS_INFORMATION_CLASS, *PFS_INFORMATION_CLASS;

typedef struct _FILE_FS_DEVICE_INFORMATION {
  DEVICE_TYPE  DeviceType;
  ULONG  Characteristics;
} FILE_FS_DEVICE_INFORMATION, *PFILE_FS_DEVICE_INFORMATION;

typedef struct _FILE_FULL_EA_INFORMATION {
  ULONG  NextEntryOffset;
  UCHAR  Flags;
  UCHAR  EaNameLength;
  USHORT  EaValueLength;
  CHAR  EaName[1];
} FILE_FULL_EA_INFORMATION, *PFILE_FULL_EA_INFORMATION;

typedef ULONG_PTR ERESOURCE_THREAD;
typedef ERESOURCE_THREAD *PERESOURCE_THREAD;

typedef struct _OWNER_ENTRY {
  ERESOURCE_THREAD  OwnerThread;
  _ANONYMOUS_UNION union {
      LONG  OwnerCount;
      ULONG  TableSize;
  } DUMMYUNIONNAME;
} OWNER_ENTRY, *POWNER_ENTRY;

/* ERESOURCE.Flag */

#define ResourceNeverExclusive            0x0010
#define ResourceReleaseByOtherThread      0x0020
#define ResourceOwnedExclusive            0x0080

#define RESOURCE_HASH_TABLE_SIZE          64

typedef struct _ERESOURCE {
  LIST_ENTRY  SystemResourcesList;
  POWNER_ENTRY  OwnerTable;
  SHORT  ActiveCount;
  USHORT  Flag;
  PKSEMAPHORE  SharedWaiters;
  PKEVENT  ExclusiveWaiters;
  OWNER_ENTRY  OwnerThreads[2];
  ULONG  ContentionCount;
  USHORT  NumberOfSharedWaiters;
  USHORT  NumberOfExclusiveWaiters;
  _ANONYMOUS_UNION union {
    PVOID  Address;
    ULONG_PTR  CreatorBackTraceIndex;
  } DUMMYUNIONNAME;
  KSPIN_LOCK  SpinLock;
} ERESOURCE, *PERESOURCE;

/* NOTE: PVOID for methods to avoid 'assignment from incompatible pointer type' warning */
typedef struct _DRIVER_EXTENSION {
  struct _DRIVER_OBJECT  *DriverObject;
  PVOID  AddDevice;
  ULONG  Count;
  UNICODE_STRING  ServiceKeyName;
} DRIVER_EXTENSION, *PDRIVER_EXTENSION;

typedef BOOLEAN 
(DDKAPI *PFAST_IO_CHECK_IF_POSSIBLE)(
  /*IN*/ struct _FILE_OBJECT  *FileObject,
  /*IN*/ PLARGE_INTEGER  FileOffset,
  /*IN*/ ULONG  Length,
  /*IN*/ BOOLEAN  Wait,
  /*IN*/ ULONG  LockKey,
  /*IN*/ BOOLEAN  CheckForReadOperation,
  /*OUT*/ PIO_STATUS_BLOCK  IoStatus,
  /*IN*/ struct _DEVICE_OBJECT  *DeviceObject);

typedef BOOLEAN 
(DDKAPI *PFAST_IO_READ)(
  /*IN*/ struct _FILE_OBJECT  *FileObject,
  /*IN*/ PLARGE_INTEGER  FileOffset,
  /*IN*/ ULONG  Length,
  /*IN*/ BOOLEAN  Wait,
  /*IN*/ ULONG  LockKey,
  /*OUT*/ PVOID  Buffer,
  /*OUT*/ PIO_STATUS_BLOCK  IoStatus,
  /*IN*/ struct _DEVICE_OBJECT  *DeviceObject);

typedef BOOLEAN 
(DDKAPI *PFAST_IO_WRITE)(
  /*IN*/ struct _FILE_OBJECT  *FileObject,
  /*IN*/ PLARGE_INTEGER  FileOffset,
  /*IN*/ ULONG  Length,
  /*IN*/ BOOLEAN  Wait,
  /*IN*/ ULONG  LockKey,
  /*IN*/ PVOID  Buffer,
  /*OUT*/ PIO_STATUS_BLOCK  IoStatus,
  /*IN*/ struct _DEVICE_OBJECT  *DeviceObject);

typedef BOOLEAN 
(DDKAPI *PFAST_IO_QUERY_BASIC_INFO)(
  /*IN*/ struct _FILE_OBJECT  *FileObject,
  /*IN*/ BOOLEAN  Wait,
  /*OUT*/ PFILE_BASIC_INFORMATION  Buffer,
  /*OUT*/ PIO_STATUS_BLOCK  IoStatus,
  /*IN*/ struct _DEVICE_OBJECT  *DeviceObject);

typedef BOOLEAN 
(DDKAPI *PFAST_IO_QUERY_STANDARD_INFO)(
  /*IN*/ struct _FILE_OBJECT  *FileObject,
  /*IN*/ BOOLEAN  Wait,
  /*OUT*/ PFILE_STANDARD_INFORMATION  Buffer,
  /*OUT*/ PIO_STATUS_BLOCK  IoStatus,
  /*IN*/ struct _DEVICE_OBJECT  *DeviceObject);

typedef BOOLEAN 
(DDKAPI *PFAST_IO_LOCK)(
  /*IN*/ struct _FILE_OBJECT  *FileObject,
  /*IN*/ PLARGE_INTEGER  FileOffset,
  /*IN*/ PLARGE_INTEGER  Length,
  PEPROCESS  ProcessId,
  ULONG  Key,
  BOOLEAN  FailImmediately,
  BOOLEAN  ExclusiveLock,
  /*OUT*/ PIO_STATUS_BLOCK  IoStatus,
  /*IN*/ struct _DEVICE_OBJECT  *DeviceObject);

typedef BOOLEAN 
(DDKAPI *PFAST_IO_UNLOCK_SINGLE)(
  /*IN*/ struct _FILE_OBJECT  *FileObject,
  /*IN*/ PLARGE_INTEGER  FileOffset,
  /*IN*/ PLARGE_INTEGER  Length,
  PEPROCESS  ProcessId,
  ULONG  Key,
  /*OUT*/ PIO_STATUS_BLOCK  IoStatus,
  /*IN*/ struct _DEVICE_OBJECT  *DeviceObject);

typedef BOOLEAN 
(DDKAPI *PFAST_IO_UNLOCK_ALL)(
  /*IN*/ struct _FILE_OBJECT  *FileObject,
  PEPROCESS  ProcessId,
  /*OUT*/ PIO_STATUS_BLOCK  IoStatus,
  /*IN*/ struct _DEVICE_OBJECT  *DeviceObject);

typedef BOOLEAN 
(DDKAPI *PFAST_IO_UNLOCK_ALL_BY_KEY)(
  /*IN*/ struct _FILE_OBJECT  *FileObject,
  PVOID  ProcessId,
  ULONG  Key,
  /*OUT*/ PIO_STATUS_BLOCK  IoStatus,
  /*IN*/ struct _DEVICE_OBJECT  *DeviceObject);

typedef BOOLEAN 
(DDKAPI *PFAST_IO_DEVICE_CONTROL)(
  /*IN*/ struct _FILE_OBJECT  *FileObject,
  /*IN*/ BOOLEAN  Wait,
  /*IN*/ PVOID  InputBuffer  /*OPTIONAL*/,
  /*IN*/ ULONG  InputBufferLength,
  /*OUT*/ PVOID  OutputBuffer  /*OPTIONAL*/,
  /*IN*/ ULONG  OutputBufferLength,
  /*IN*/ ULONG  IoControlCode,
  /*OUT*/ PIO_STATUS_BLOCK  IoStatus,
  /*IN*/ struct _DEVICE_OBJECT  *DeviceObject);

typedef VOID 
(DDKAPI *PFAST_IO_ACQUIRE_FILE)(
  /*IN*/ struct _FILE_OBJECT  *FileObject);

typedef VOID 
(DDKAPI *PFAST_IO_RELEASE_FILE)(
  /*IN*/ struct _FILE_OBJECT  *FileObject);

typedef VOID 
(DDKAPI *PFAST_IO_DETACH_DEVICE)(
  /*IN*/ struct _DEVICE_OBJECT  *SourceDevice,
  /*IN*/ struct _DEVICE_OBJECT  *TargetDevice);

typedef BOOLEAN 
(DDKAPI *PFAST_IO_QUERY_NETWORK_OPEN_INFO)(
  /*IN*/ struct _FILE_OBJECT  *FileObject,
  /*IN*/ BOOLEAN  Wait,
  /*OUT*/ struct _FILE_NETWORK_OPEN_INFORMATION  *Buffer,
  /*OUT*/ struct _IO_STATUS_BLOCK  *IoStatus,
  /*IN*/ struct _DEVICE_OBJECT  *DeviceObject);

typedef NTSTATUS 
(DDKAPI *PFAST_IO_ACQUIRE_FOR_MOD_WRITE)(
  /*IN*/ struct _FILE_OBJECT  *FileObject,
  /*IN*/ PLARGE_INTEGER  EndingOffset,
  /*OUT*/ struct _ERESOURCE  **ResourceToRelease,
  /*IN*/ struct _DEVICE_OBJECT  *DeviceObject);

typedef BOOLEAN 
(DDKAPI *PFAST_IO_MDL_READ)(
  /*IN*/ struct _FILE_OBJECT  *FileObject,
  /*IN*/ PLARGE_INTEGER  FileOffset,
  /*IN*/ ULONG  Length,
  /*IN*/ ULONG  LockKey,
  /*OUT*/ PMDL  *MdlChain,
  /*OUT*/ PIO_STATUS_BLOCK  IoStatus,
  /*IN*/ struct _DEVICE_OBJECT  *DeviceObject);

typedef BOOLEAN 
(DDKAPI *PFAST_IO_MDL_READ_COMPLETE)(
  /*IN*/ struct _FILE_OBJECT *FileObject,
  /*IN*/ PMDL MdlChain,
  /*IN*/ struct _DEVICE_OBJECT *DeviceObject);

typedef BOOLEAN 
(DDKAPI *PFAST_IO_PREPARE_MDL_WRITE)(
  /*IN*/ struct _FILE_OBJECT  *FileObject,
  /*IN*/ PLARGE_INTEGER  FileOffset,
  /*IN*/ ULONG  Length,
  /*IN*/ ULONG  LockKey,
  /*OUT*/ PMDL  *MdlChain,
  /*OUT*/ PIO_STATUS_BLOCK  IoStatus,
  /*IN*/ struct _DEVICE_OBJECT  *DeviceObject);

typedef BOOLEAN 
(DDKAPI *PFAST_IO_MDL_WRITE_COMPLETE)(
  /*IN*/ struct _FILE_OBJECT  *FileObject,
  /*IN*/ PLARGE_INTEGER  FileOffset,
  /*IN*/ PMDL  MdlChain,
  /*IN*/ struct _DEVICE_OBJECT  *DeviceObject);

typedef BOOLEAN 
(DDKAPI *PFAST_IO_READ_COMPRESSED)(
  /*IN*/ struct _FILE_OBJECT  *FileObject,
  /*IN*/ PLARGE_INTEGER  FileOffset,
  /*IN*/ ULONG  Length,
  /*IN*/ ULONG  LockKey,
  /*OUT*/ PVOID  Buffer,
  /*OUT*/ PMDL  *MdlChain,
  /*OUT*/ PIO_STATUS_BLOCK  IoStatus,
  /*OUT*/ struct _COMPRESSED_DATA_INFO  *CompressedDataInfo,
  /*IN*/ ULONG  CompressedDataInfoLength,
  /*IN*/ struct _DEVICE_OBJECT  *DeviceObject);

typedef BOOLEAN 
(DDKAPI *PFAST_IO_WRITE_COMPRESSED)(
  /*IN*/ struct _FILE_OBJECT  *FileObject,
  /*IN*/ PLARGE_INTEGER  FileOffset,
  /*IN*/ ULONG  Length,
  /*IN*/ ULONG  LockKey,
  /*IN*/ PVOID  Buffer,
  /*OUT*/ PMDL  *MdlChain,
  /*OUT*/ PIO_STATUS_BLOCK  IoStatus,
  /*IN*/ struct _COMPRESSED_DATA_INFO  *CompressedDataInfo,
  /*IN*/ ULONG  CompressedDataInfoLength,
  /*IN*/ struct _DEVICE_OBJECT  *DeviceObject);

typedef BOOLEAN 
(DDKAPI *PFAST_IO_MDL_READ_COMPLETE_COMPRESSED)(
  /*IN*/ struct _FILE_OBJECT  *FileObject,
  /*IN*/ PMDL  MdlChain,
  /*IN*/ struct _DEVICE_OBJECT  *DeviceObject);

typedef BOOLEAN 
(DDKAPI *PFAST_IO_MDL_WRITE_COMPLETE_COMPRESSED)(
  /*IN*/ struct _FILE_OBJECT  *FileObject,
  /*IN*/ PLARGE_INTEGER  FileOffset,
  /*IN*/ PMDL  MdlChain,
  /*IN*/ struct _DEVICE_OBJECT  *DeviceObject);

typedef BOOLEAN 
(DDKAPI *PFAST_IO_QUERY_OPEN)(
  /*IN*/ struct _IRP  *Irp,
  /*OUT*/ PFILE_NETWORK_OPEN_INFORMATION  NetworkInformation,
  /*IN*/ struct _DEVICE_OBJECT  *DeviceObject);

typedef NTSTATUS 
(DDKAPI *PFAST_IO_RELEASE_FOR_MOD_WRITE)(
  /*IN*/ struct _FILE_OBJECT  *FileObject,
  /*IN*/ struct _ERESOURCE  *ResourceToRelease,
  /*IN*/ struct _DEVICE_OBJECT  *DeviceObject);

typedef NTSTATUS 
(DDKAPI *PFAST_IO_ACQUIRE_FOR_CCFLUSH)(
  /*IN*/ struct _FILE_OBJECT  *FileObject,
  /*IN*/ struct _DEVICE_OBJECT  *DeviceObject);

typedef NTSTATUS 
(DDKAPI *PFAST_IO_RELEASE_FOR_CCFLUSH) (
  /*IN*/ struct _FILE_OBJECT  *FileObject,
  /*IN*/ struct _DEVICE_OBJECT  *DeviceObject);

typedef struct _FAST_IO_DISPATCH {
  ULONG  SizeOfFastIoDispatch;
  PFAST_IO_CHECK_IF_POSSIBLE  FastIoCheckIfPossible;
  PFAST_IO_READ  FastIoRead;
  PFAST_IO_WRITE  FastIoWrite;
  PFAST_IO_QUERY_BASIC_INFO  FastIoQueryBasicInfo;
  PFAST_IO_QUERY_STANDARD_INFO  FastIoQueryStandardInfo;
  PFAST_IO_LOCK  FastIoLock;
  PFAST_IO_UNLOCK_SINGLE  FastIoUnlockSingle;
  PFAST_IO_UNLOCK_ALL  FastIoUnlockAll;
  PFAST_IO_UNLOCK_ALL_BY_KEY  FastIoUnlockAllByKey;
  PFAST_IO_DEVICE_CONTROL  FastIoDeviceControl;
  PFAST_IO_ACQUIRE_FILE  AcquireFileForNtCreateSection;
  PFAST_IO_RELEASE_FILE  ReleaseFileForNtCreateSection;
  PFAST_IO_DETACH_DEVICE  FastIoDetachDevice;
  PFAST_IO_QUERY_NETWORK_OPEN_INFO  FastIoQueryNetworkOpenInfo;
  PFAST_IO_ACQUIRE_FOR_MOD_WRITE  AcquireForModWrite;
  PFAST_IO_MDL_READ  MdlRead;
  PFAST_IO_MDL_READ_COMPLETE  MdlReadComplete;
  PFAST_IO_PREPARE_MDL_WRITE  PrepareMdlWrite;
  PFAST_IO_MDL_WRITE_COMPLETE  MdlWriteComplete;
  PFAST_IO_READ_COMPRESSED  FastIoReadCompressed;
  PFAST_IO_WRITE_COMPRESSED  FastIoWriteCompressed;
  PFAST_IO_MDL_READ_COMPLETE_COMPRESSED  MdlReadCompleteCompressed;
  PFAST_IO_MDL_WRITE_COMPLETE_COMPRESSED  MdlWriteCompleteCompressed;
  PFAST_IO_QUERY_OPEN  FastIoQueryOpen;
  PFAST_IO_RELEASE_FOR_MOD_WRITE  ReleaseForModWrite;
  PFAST_IO_ACQUIRE_FOR_CCFLUSH  AcquireForCcFlush;
  PFAST_IO_RELEASE_FOR_CCFLUSH  ReleaseForCcFlush;
} FAST_IO_DISPATCH, *PFAST_IO_DISPATCH;

typedef struct _DRIVER_OBJECT {
  CSHORT  Type;
  CSHORT  Size;
  PDEVICE_OBJECT  DeviceObject;
  ULONG  Flags;
  PVOID  DriverStart;
  ULONG  DriverSize;
  PVOID  DriverSection;
  PDRIVER_EXTENSION  DriverExtension;
  UNICODE_STRING  DriverName;
  PUNICODE_STRING  HardwareDatabase;
  PFAST_IO_DISPATCH  FastIoDispatch;
  PDRIVER_INITIALIZE  DriverInit;
  PDRIVER_STARTIO  DriverStartIo;
  PDRIVER_UNLOAD  DriverUnload;
  PDRIVER_DISPATCH  MajorFunction[IRP_MJ_MAXIMUM_FUNCTION + 1];
} DRIVER_OBJECT;
typedef struct _DRIVER_OBJECT *PDRIVER_OBJECT;

typedef struct _SECTION_OBJECT_POINTERS {
  PVOID  DataSectionObject;
  PVOID  SharedCacheMap;
  PVOID  ImageSectionObject;
} SECTION_OBJECT_POINTERS, *PSECTION_OBJECT_POINTERS;

typedef struct _IO_COMPLETION_CONTEXT {
  PVOID  Port;
  PVOID  Key;
} IO_COMPLETION_CONTEXT, *PIO_COMPLETION_CONTEXT;

/* FILE_OBJECT.Flags */

#define FO_FILE_OPEN                      0x00000001
#define FO_SYNCHRONOUS_IO                 0x00000002
#define FO_ALERTABLE_IO                   0x00000004
#define FO_NO_INTERMEDIATE_BUFFERING      0x00000008
#define FO_WRITE_THROUGH                  0x00000010
#define FO_SEQUENTIAL_ONLY                0x00000020
#define FO_CACHE_SUPPORTED                0x00000040
#define FO_NAMED_PIPE                     0x00000080
#define FO_STREAM_FILE                    0x00000100
#define FO_MAILSLOT                       0x00000200
#define FO_GENERATE_AUDIT_ON_CLOSE        0x00000400
#define FO_DIRECT_DEVICE_OPEN             0x00000800
#define FO_FILE_MODIFIED                  0x00001000
#define FO_FILE_SIZE_CHANGED              0x00002000
#define FO_CLEANUP_COMPLETE               0x00004000
#define FO_TEMPORARY_FILE                 0x00008000
#define FO_DELETE_ON_CLOSE                0x00010000
#define FO_OPENED_CASE_SENSITIVE          0x00020000
#define FO_HANDLE_CREATED                 0x00040000
#define FO_FILE_FAST_IO_READ              0x00080000
#define FO_RANDOM_ACCESS                  0x00100000
#define FO_FILE_OPEN_CANCELLED            0x00200000
#define FO_VOLUME_OPEN                    0x00400000
#define FO_FILE_OBJECT_HAS_EXTENSION      0x00800000
#define FO_REMOTE_ORIGIN                  0x01000000

typedef struct _FILE_OBJECT {
  CSHORT  Type;
  CSHORT  Size;
  PDEVICE_OBJECT  DeviceObject;
  PVPB  Vpb;
  PVOID  FsContext;
  PVOID  FsContext2;
  PSECTION_OBJECT_POINTERS  SectionObjectPointer;
  PVOID  PrivateCacheMap;
  NTSTATUS  FinalStatus;
  struct _FILE_OBJECT  *RelatedFileObject;
  BOOLEAN  LockOperation;
  BOOLEAN  DeletePending;
  BOOLEAN  ReadAccess;
  BOOLEAN  WriteAccess;
  BOOLEAN  DeleteAccess;
  BOOLEAN  SharedRead;
  BOOLEAN  SharedWrite;
  BOOLEAN  SharedDelete;
  ULONG  Flags;
  UNICODE_STRING  FileName;
  LARGE_INTEGER  CurrentByteOffset;
  ULONG  Waiters;
  ULONG  Busy;
  PVOID  LastLock;
  KEVENT  Lock;
  KEVENT  Event;
  PIO_COMPLETION_CONTEXT  CompletionContext;
} FILE_OBJECT;
typedef struct _FILE_OBJECT *PFILE_OBJECT;

typedef enum _SECURITY_OPERATION_CODE {
  SetSecurityDescriptor,
  QuerySecurityDescriptor,
  DeleteSecurityDescriptor,
  AssignSecurityDescriptor
} SECURITY_OPERATION_CODE, *PSECURITY_OPERATION_CODE;

#define INITIAL_PRIVILEGE_COUNT           3

typedef struct _INITIAL_PRIVILEGE_SET {
  ULONG  PrivilegeCount;
  ULONG  Control;
  LUID_AND_ATTRIBUTES  Privilege[INITIAL_PRIVILEGE_COUNT];
} INITIAL_PRIVILEGE_SET, * PINITIAL_PRIVILEGE_SET;

typedef struct _SECURITY_SUBJECT_CONTEXT {
  PACCESS_TOKEN  ClientToken;
  SECURITY_IMPERSONATION_LEVEL  ImpersonationLevel;
  PACCESS_TOKEN  PrimaryToken;
  PVOID  ProcessAuditId;
} SECURITY_SUBJECT_CONTEXT, *PSECURITY_SUBJECT_CONTEXT;

#include <pshpack4.h>
typedef struct _ACCESS_STATE {
  LUID  OperationID;
  BOOLEAN  SecurityEvaluated;
  BOOLEAN  GenerateAudit;
  BOOLEAN  GenerateOnClose;
  BOOLEAN  PrivilegesAllocated;
  ULONG  Flags;
  ACCESS_MASK  RemainingDesiredAccess;
  ACCESS_MASK  PreviouslyGrantedAccess;
  ACCESS_MASK  OriginalDesiredAccess;
  SECURITY_SUBJECT_CONTEXT  SubjectSecurityContext;
  PSECURITY_DESCRIPTOR  SecurityDescriptor;
  PVOID  AuxData;
  union {
    INITIAL_PRIVILEGE_SET  InitialPrivilegeSet;
    PRIVILEGE_SET  PrivilegeSet;
  } Privileges;

  BOOLEAN  AuditPrivileges;
  UNICODE_STRING  ObjectName;
  UNICODE_STRING  ObjectTypeName;
} ACCESS_STATE, *PACCESS_STATE;
#include <poppack.h>

typedef struct _IO_SECURITY_CONTEXT {
  PSECURITY_QUALITY_OF_SERVICE  SecurityQos;
  PACCESS_STATE  AccessState;
  ACCESS_MASK  DesiredAccess;
  ULONG  FullCreateOptions;
} IO_SECURITY_CONTEXT, *PIO_SECURITY_CONTEXT;

struct _IO_CSQ;

typedef struct _IO_CSQ_IRP_CONTEXT {
  ULONG  Type;
  struct _IRP  *Irp;
  struct _IO_CSQ  *Csq;
} IO_CSQ_IRP_CONTEXT, *PIO_CSQ_IRP_CONTEXT;

typedef VOID 
(DDKAPI *PIO_CSQ_INSERT_IRP)(
  /*IN*/ struct _IO_CSQ  *Csq,
  /*IN*/ PIRP  Irp);

typedef VOID 
(DDKAPI *PIO_CSQ_REMOVE_IRP)(
  /*IN*/ struct _IO_CSQ  *Csq,
  /*IN*/ PIRP  Irp);

typedef PIRP 
(DDKAPI *PIO_CSQ_PEEK_NEXT_IRP)(
  /*IN*/ struct _IO_CSQ  *Csq,
  /*IN*/ PIRP  Irp,
  /*IN*/ PVOID  PeekContext);

typedef VOID 
(DDKAPI *PIO_CSQ_ACQUIRE_LOCK)(
  /*IN*/ struct _IO_CSQ  *Csq,
  /*OUT*/ PKIRQL  Irql);

typedef VOID 
(DDKAPI *PIO_CSQ_RELEASE_LOCK)(
  /*IN*/ struct _IO_CSQ  *Csq,
  /*IN*/ KIRQL  Irql);

typedef VOID 
(DDKAPI *PIO_CSQ_COMPLETE_CANCELED_IRP)(
  /*IN*/ struct _IO_CSQ  *Csq,
  /*IN*/ PIRP  Irp);

typedef struct _IO_CSQ {
  ULONG  Type;
  PIO_CSQ_INSERT_IRP  CsqInsertIrp;
  PIO_CSQ_REMOVE_IRP  CsqRemoveIrp;
  PIO_CSQ_PEEK_NEXT_IRP  CsqPeekNextIrp;
  PIO_CSQ_ACQUIRE_LOCK  CsqAcquireLock;
  PIO_CSQ_RELEASE_LOCK  CsqReleaseLock;
  PIO_CSQ_COMPLETE_CANCELED_IRP  CsqCompleteCanceledIrp;
  PVOID  ReservePointer;
} IO_CSQ, *PIO_CSQ;

#include <pshpack4.h>
typedef struct _IO_STACK_LOCATION {
  UCHAR  MajorFunction;
  UCHAR  MinorFunction;
  UCHAR  Flags;
  UCHAR  Control;
  union {
    struct {
      PIO_SECURITY_CONTEXT  SecurityContext;
      ULONG  Options;
      USHORT POINTER_ALIGNMENT  FileAttributes;
      USHORT  ShareAccess;
      ULONG POINTER_ALIGNMENT  EaLength;
    } Create;
    struct {
      ULONG  Length;
      ULONG POINTER_ALIGNMENT  Key;
      LARGE_INTEGER  ByteOffset;
    } Read;
    struct {
      ULONG  Length;
      ULONG POINTER_ALIGNMENT  Key;
      LARGE_INTEGER  ByteOffset;
    } Write;
    struct {
      ULONG  Length;
      FILE_INFORMATION_CLASS POINTER_ALIGNMENT  FileInformationClass;
    } QueryFile;
    struct {
      ULONG  Length;
      FILE_INFORMATION_CLASS POINTER_ALIGNMENT  FileInformationClass;
      PFILE_OBJECT  FileObject;
      _ANONYMOUS_UNION union {
        _ANONYMOUS_STRUCT struct {
          BOOLEAN  ReplaceIfExists;
          BOOLEAN  AdvanceOnly;
        } DUMMYSTRUCTNAME;
        ULONG  ClusterCount;
        HANDLE  DeleteHandle;
      } DUMMYUNIONNAME;
    } SetFile;
    struct {
      ULONG  Length;
      FS_INFORMATION_CLASS POINTER_ALIGNMENT  FsInformationClass;
    } QueryVolume;
    struct {
      ULONG  OutputBufferLength;
      ULONG POINTER_ALIGNMENT  InputBufferLength;
      ULONG POINTER_ALIGNMENT  IoControlCode;
      PVOID  Type3InputBuffer;
    } DeviceIoControl;
    struct {
      SECURITY_INFORMATION  SecurityInformation;
      ULONG POINTER_ALIGNMENT  Length;
    } QuerySecurity;
    struct {
      SECURITY_INFORMATION  SecurityInformation;
      PSECURITY_DESCRIPTOR  SecurityDescriptor;
    } SetSecurity;
    struct {
      PVPB  Vpb;
      PDEVICE_OBJECT  DeviceObject;
    } MountVolume;
    struct {
      PVPB  Vpb;
      PDEVICE_OBJECT  DeviceObject;
    } VerifyVolume;
    struct {
      struct _SCSI_REQUEST_BLOCK  *Srb;
    } Scsi;
    struct {
      DEVICE_RELATION_TYPE  Type;
    } QueryDeviceRelations;
    struct {
      CONST GUID  *InterfaceType;
      USHORT  Size;
      USHORT  Version;
      PINTERFACE  Interface;
      PVOID  InterfaceSpecificData;
    } QueryInterface;
    struct {
      PDEVICE_CAPABILITIES  Capabilities;
    } DeviceCapabilities;
    struct {
      PIO_RESOURCE_REQUIREMENTS_LIST  IoResourceRequirementList;
    } FilterResourceRequirements;
    struct {
      ULONG  WhichSpace;
      PVOID  Buffer;
      ULONG  Offset;
      ULONG POINTER_ALIGNMENT  Length;
    } ReadWriteConfig;
    struct {
      BOOLEAN  Lock;
    } SetLock;
    struct {
      BUS_QUERY_ID_TYPE  IdType;
    } QueryId;
    struct {
      DEVICE_TEXT_TYPE  DeviceTextType;
      LCID POINTER_ALIGNMENT  LocaleId;
    } QueryDeviceText;
    struct {
      BOOLEAN  InPath;
      BOOLEAN  Reserved[3];
      DEVICE_USAGE_NOTIFICATION_TYPE POINTER_ALIGNMENT  Type;
    } UsageNotification;
    struct {
      SYSTEM_POWER_STATE  PowerState;
    } WaitWake;
    struct {
      PPOWER_SEQUENCE  PowerSequence;
    } PowerSequence;
    struct {
      ULONG  SystemContext;
      POWER_STATE_TYPE POINTER_ALIGNMENT  Type;
      POWER_STATE POINTER_ALIGNMENT  State;
      POWER_ACTION POINTER_ALIGNMENT  ShutdownType;
    } Power;
    struct {
      PCM_RESOURCE_LIST  AllocatedResources;
      PCM_RESOURCE_LIST  AllocatedResourcesTranslated;
    } StartDevice;
    struct {
      ULONG_PTR  ProviderId;
      PVOID  DataPath;
      ULONG  BufferSize;
      PVOID  Buffer;
    } WMI;
    struct {
      PVOID  Argument1;
      PVOID  Argument2;
      PVOID  Argument3;
      PVOID  Argument4;
    } Others;
  } Parameters;
  PDEVICE_OBJECT  DeviceObject;
  PFILE_OBJECT  FileObject;
  PIO_COMPLETION_ROUTINE  CompletionRoutine;
  PVOID  Context;
} IO_STACK_LOCATION, *PIO_STACK_LOCATION;
#include <poppack.h>

/* IO_STACK_LOCATION.Control */

#define SL_PENDING_RETURNED               0x01
#define SL_INVOKE_ON_CANCEL               0x20
#define SL_INVOKE_ON_SUCCESS              0x40
#define SL_INVOKE_ON_ERROR                0x80

typedef enum _KEY_INFORMATION_CLASS {
  KeyBasicInformation,
  KeyNodeInformation,
  KeyFullInformation,
  KeyNameInformation,
  KeyCachedInformation,
  KeyFlagsInformation
} KEY_INFORMATION_CLASS;

typedef struct _KEY_BASIC_INFORMATION {
  LARGE_INTEGER  LastWriteTime;
  ULONG  TitleIndex;
  ULONG  NameLength;
  WCHAR  Name[1];
} KEY_BASIC_INFORMATION, *PKEY_BASIC_INFORMATION;

typedef struct _KEY_FULL_INFORMATION {
  LARGE_INTEGER  LastWriteTime;
  ULONG  TitleIndex;
  ULONG  ClassOffset;
  ULONG  ClassLength;
  ULONG  SubKeys;
  ULONG  MaxNameLen;
  ULONG  MaxClassLen;
  ULONG  Values;
  ULONG  MaxValueNameLen;
  ULONG  MaxValueDataLen;
  WCHAR  Class[1];
} KEY_FULL_INFORMATION, *PKEY_FULL_INFORMATION;

typedef struct _KEY_NODE_INFORMATION {
  LARGE_INTEGER  LastWriteTime;
  ULONG  TitleIndex;
  ULONG  ClassOffset;
  ULONG  ClassLength;
  ULONG  NameLength;
  WCHAR  Name[1];
} KEY_NODE_INFORMATION, *PKEY_NODE_INFORMATION;

typedef struct _KEY_VALUE_BASIC_INFORMATION {
  ULONG  TitleIndex;
  ULONG  Type;
  ULONG  NameLength;
  WCHAR  Name[1];
} KEY_VALUE_BASIC_INFORMATION, *PKEY_VALUE_BASIC_INFORMATION;

typedef struct _KEY_VALUE_FULL_INFORMATION {
  ULONG  TitleIndex;
  ULONG  Type;
  ULONG  DataOffset;
  ULONG  DataLength;
  ULONG  NameLength;
  WCHAR  Name[1];
} KEY_VALUE_FULL_INFORMATION, *PKEY_VALUE_FULL_INFORMATION;

typedef struct _KEY_VALUE_PARTIAL_INFORMATION {
  ULONG  TitleIndex;
  ULONG  Type;
  ULONG  DataLength;
  UCHAR  Data[1];
} KEY_VALUE_PARTIAL_INFORMATION, *PKEY_VALUE_PARTIAL_INFORMATION;

typedef struct _KEY_VALUE_PARTIAL_INFORMATION_ALIGN64 {
  ULONG  Type;
  ULONG  DataLength;
  UCHAR  Data[1];
} KEY_VALUE_PARTIAL_INFORMATION_ALIGN64, *PKEY_VALUE_PARTIAL_INFORMATION_ALIGN64;

typedef struct _KEY_VALUE_ENTRY {
  PUNICODE_STRING  ValueName;
  ULONG  DataLength;
  ULONG  DataOffset;
  ULONG  Type;
} KEY_VALUE_ENTRY, *PKEY_VALUE_ENTRY;

typedef enum _KEY_VALUE_INFORMATION_CLASS {
  KeyValueBasicInformation,
  KeyValueFullInformation,
  KeyValuePartialInformation,
  KeyValueFullInformationAlign64,
  KeyValuePartialInformationAlign64
} KEY_VALUE_INFORMATION_CLASS;

/* KEY_VALUE_Xxx.Type */

//#define REG_NONE                           0
//#define REG_SZ                             1
//#define REG_EXPAND_SZ                      2
//#define REG_BINARY                         3
//#define REG_DWORD                          4
//#define REG_DWORD_LITTLE_ENDIAN            4
//#define REG_DWORD_BIG_ENDIAN               5
//#define REG_LINK                           6
//#define REG_MULTI_SZ                       7
//#define REG_RESOURCE_LIST                  8
//#define REG_FULL_RESOURCE_DESCRIPTOR       9
//#define REG_RESOURCE_REQUIREMENTS_LIST    10
//#define REG_QWORD                         11
//#define REG_QWORD_LITTLE_ENDIAN           11

#define PCI_TYPE0_ADDRESSES               6
#define PCI_TYPE1_ADDRESSES               2
#define PCI_TYPE2_ADDRESSES               5

typedef struct _PCI_COMMON_CONFIG {
  USHORT  VendorID;
  USHORT  DeviceID;
  USHORT  Command;
  USHORT  Status;
  UCHAR  RevisionID;
  UCHAR  ProgIf;
  UCHAR  SubClass;
  UCHAR  BaseClass;
  UCHAR  CacheLineSize;
  UCHAR  LatencyTimer;
  UCHAR  HeaderType;
  UCHAR  BIST;
  union {
    struct _PCI_HEADER_TYPE_0 {
      ULONG  BaseAddresses[PCI_TYPE0_ADDRESSES];
      ULONG  CIS;
      USHORT  SubVendorID;
      USHORT  SubSystemID;
      ULONG  ROMBaseAddress;
      UCHAR  CapabilitiesPtr;
      UCHAR  Reserved1[3];
      ULONG  Reserved2;
      UCHAR  InterruptLine;
      UCHAR  InterruptPin;
      UCHAR  MinimumGrant;
      UCHAR  MaximumLatency;
    } type0;
      struct _PCI_HEADER_TYPE_1 {
        ULONG  BaseAddresses[PCI_TYPE1_ADDRESSES];
        UCHAR  PrimaryBus;
        UCHAR  SecondaryBus;
        UCHAR  SubordinateBus;
        UCHAR  SecondaryLatency;
        UCHAR  IOBase;
        UCHAR  IOLimit;
        USHORT  SecondaryStatus;
        USHORT  MemoryBase;
        USHORT  MemoryLimit;
        USHORT  PrefetchBase;
        USHORT  PrefetchLimit;
        ULONG  PrefetchBaseUpper32;
        ULONG  PrefetchLimitUpper32;
        USHORT  IOBaseUpper16;
        USHORT  IOLimitUpper16;
        UCHAR  CapabilitiesPtr;
        UCHAR  Reserved1[3];
        ULONG  ROMBaseAddress;
        UCHAR  InterruptLine;
        UCHAR  InterruptPin;
        USHORT  BridgeControl;
      } type1;
      struct _PCI_HEADER_TYPE_2 {
        ULONG  SocketRegistersBaseAddress;
        UCHAR  CapabilitiesPtr;
        UCHAR  Reserved;
        USHORT  SecondaryStatus;
        UCHAR  PrimaryBus;
        UCHAR  SecondaryBus;
        UCHAR  SubordinateBus;
        UCHAR  SecondaryLatency;
        struct {
          ULONG  Base;
          ULONG  Limit;
        } Range[PCI_TYPE2_ADDRESSES - 1];
        UCHAR  InterruptLine;
        UCHAR  InterruptPin;
        USHORT  BridgeControl;
      } type2;
  } u;
  UCHAR  DeviceSpecific[192];
} PCI_COMMON_CONFIG, *PPCI_COMMON_CONFIG;

/* PCI_COMMON_CONFIG.Command */

#define PCI_ENABLE_IO_SPACE               0x0001
#define PCI_ENABLE_MEMORY_SPACE           0x0002
#define PCI_ENABLE_BUS_MASTER             0x0004
#define PCI_ENABLE_SPECIAL_CYCLES         0x0008
#define PCI_ENABLE_WRITE_AND_INVALIDATE   0x0010
#define PCI_ENABLE_VGA_COMPATIBLE_PALETTE 0x0020
#define PCI_ENABLE_PARITY                 0x0040
#define PCI_ENABLE_WAIT_CYCLE             0x0080
#define PCI_ENABLE_SERR                   0x0100
#define PCI_ENABLE_FAST_BACK_TO_BACK      0x0200

/* PCI_COMMON_CONFIG.Status */

#define PCI_STATUS_CAPABILITIES_LIST      0x0010
#define PCI_STATUS_66MHZ_CAPABLE          0x0020
#define PCI_STATUS_UDF_SUPPORTED          0x0040
#define PCI_STATUS_FAST_BACK_TO_BACK      0x0080
#define PCI_STATUS_DATA_PARITY_DETECTED   0x0100
#define PCI_STATUS_DEVSEL                 0x0600
#define PCI_STATUS_SIGNALED_TARGET_ABORT  0x0800
#define PCI_STATUS_RECEIVED_TARGET_ABORT  0x1000
#define PCI_STATUS_RECEIVED_MASTER_ABORT  0x2000
#define PCI_STATUS_SIGNALED_SYSTEM_ERROR  0x4000
#define PCI_STATUS_DETECTED_PARITY_ERROR  0x8000

/* PCI_COMMON_CONFIG.HeaderType */

#define PCI_MULTIFUNCTION                 0x80
#define PCI_DEVICE_TYPE                   0x00
#define PCI_BRIDGE_TYPE                   0x01
#define PCI_CARDBUS_BRIDGE_TYPE           0x02

#define PCI_CONFIGURATION_TYPE(PciData) \
  (((PPCI_COMMON_CONFIG) (PciData))->HeaderType & ~PCI_MULTIFUNCTION)

#define PCI_MULTIFUNCTION_DEVICE(PciData) \
  ((((PPCI_COMMON_CONFIG) (PciData))->HeaderType & PCI_MULTIFUNCTION) != 0)

typedef struct _PCI_SLOT_NUMBER {
  union {
    struct {
      ULONG  DeviceNumber : 5;
      ULONG  FunctionNumber : 3;
      ULONG  Reserved : 24;
    } bits;
    ULONG  AsULONG;
  } u;
} PCI_SLOT_NUMBER, *PPCI_SLOT_NUMBER;

typedef enum _POOL_TYPE {
  NonPagedPool,
  PagedPool,
  NonPagedPoolMustSucceed,
  DontUseThisType,
  NonPagedPoolCacheAligned,
  PagedPoolCacheAligned,
  NonPagedPoolCacheAlignedMustS,
	MaxPoolType,
	NonPagedPoolSession = 32,
	PagedPoolSession,
	NonPagedPoolMustSucceedSession,
	DontUseThisTypeSession,
	NonPagedPoolCacheAlignedSession,
	PagedPoolCacheAlignedSession,
	NonPagedPoolCacheAlignedMustSSession
} POOL_TYPE;

typedef enum _EX_POOL_PRIORITY {
  LowPoolPriority,
  LowPoolPrioritySpecialPoolOverrun = 8,
  LowPoolPrioritySpecialPoolUnderrun = 9,
  NormalPoolPriority = 16,
  NormalPoolPrioritySpecialPoolOverrun = 24,
  NormalPoolPrioritySpecialPoolUnderrun = 25,
  HighPoolPriority = 32,
  HighPoolPrioritySpecialPoolOverrun = 40,
  HighPoolPrioritySpecialPoolUnderrun = 41
} EX_POOL_PRIORITY;

/* PRIVILEGE_SET.Control */

//#define PRIVILEGE_SET_ALL_NECESSARY       1
/*
typedef struct _RTL_OSVERSIONINFOW {
  ULONG  dwOSVersionInfoSize;
  ULONG  dwMajorVersion;
  ULONG  dwMinorVersion;
  ULONG  dwBuildNumber;
  ULONG  dwPlatformId;
  WCHAR  szCSDVersion[128];
} RTL_OSVERSIONINFOW, *PRTL_OSVERSIONINFOW;

typedef struct _RTL_OSVERSIONINFOEXW {
  ULONG  dwOSVersionInfoSize;
  ULONG  dwMajorVersion;
  ULONG  dwMinorVersion;
  ULONG  dwBuildNumber;
  ULONG  dwPlatformId;
  WCHAR  szCSDVersion[128];
  USHORT  wServicePackMajor;
  USHORT  wServicePackMinor;
  USHORT  wSuiteMask;
  UCHAR  wProductType;
  UCHAR  wReserved;
} RTL_OSVERSIONINFOEXW, *PRTL_OSVERSIONINFOEXW;
*/
NTOSAPI
ULONGLONG
DDKAPI
VerSetConditionMask(
  /*IN*/ ULONGLONG  ConditionMask,
  /*IN*/ ULONG  TypeMask,
  /*IN*/ UCHAR  Condition);

/*
#define VER_SET_CONDITION(ConditionMask, TypeBitMask, ComparisonType)  \
        ((ConditionMask) = VerSetConditionMask((ConditionMask), \
        (TypeBitMask), (ComparisonType)))
*/
/* RtlVerifyVersionInfo() TypeMask */

#define VER_MINORVERSION                  0x0000001
#define VER_MAJORVERSION                  0x0000002
#define VER_BUILDNUMBER                   0x0000004
#define VER_PLATFORMID                    0x0000008
#define VER_SERVICEPACKMINOR              0x0000010
#define VER_SERVICEPACKMAJOR              0x0000020
#define VER_SUITENAME                     0x0000040
#define VER_PRODUCT_TYPE                  0x0000080

/* RtlVerifyVersionInfo() ComparisonType */

#define VER_EQUAL                       1
#define VER_GREATER                     2
#define VER_GREATER_EQUAL               3
#define VER_LESS                        4
#define VER_LESS_EQUAL                  5
#define VER_AND                         6
#define VER_OR                          7

#define VER_CONDITION_MASK              7
#define VER_NUM_BITS_PER_CONDITION_MASK 3

typedef struct _RTL_BITMAP {
  ULONG  SizeOfBitMap;
  PULONG  Buffer;
} RTL_BITMAP, *PRTL_BITMAP;

typedef struct _RTL_BITMAP_RUN {
    ULONG  StartingIndex;
    ULONG  NumberOfBits;
} RTL_BITMAP_RUN, *PRTL_BITMAP_RUN;

typedef NTSTATUS 
(DDKAPI *PRTL_QUERY_REGISTRY_ROUTINE)(
  /*IN*/ PWSTR  ValueName,
  /*IN*/ ULONG  ValueType,
  /*IN*/ PVOID  ValueData,
  /*IN*/ ULONG  ValueLength,
  /*IN*/ PVOID  Context,
  /*IN*/ PVOID  EntryContext);

#define RTL_REGISTRY_ABSOLUTE             0
#define RTL_REGISTRY_SERVICES             1
#define RTL_REGISTRY_CONTROL              2
#define RTL_REGISTRY_WINDOWS_NT           3
#define RTL_REGISTRY_DEVICEMAP            4
#define RTL_REGISTRY_USER                 5

/* RTL_QUERY_REGISTRY_TABLE.Flags */
#define RTL_QUERY_REGISTRY_SUBKEY         0x00000001
#define RTL_QUERY_REGISTRY_TOPKEY         0x00000002
#define RTL_QUERY_REGISTRY_REQUIRED       0x00000004
#define RTL_QUERY_REGISTRY_NOVALUE        0x00000008
#define RTL_QUERY_REGISTRY_NOEXPAND       0x00000010
#define RTL_QUERY_REGISTRY_DIRECT         0x00000020
#define RTL_QUERY_REGISTRY_DELETE         0x00000040

typedef struct _RTL_QUERY_REGISTRY_TABLE {
  PRTL_QUERY_REGISTRY_ROUTINE  QueryRoutine;
  ULONG  Flags;
  PWSTR  Name;
  PVOID  EntryContext;
  ULONG  DefaultType;
  PVOID  DefaultData;
  ULONG  DefaultLength;
} RTL_QUERY_REGISTRY_TABLE, *PRTL_QUERY_REGISTRY_TABLE;

typedef struct _TIME_FIELDS {
  CSHORT  Year;
  CSHORT  Month;
  CSHORT  Day;
  CSHORT  Hour;
  CSHORT  Minute;
  CSHORT  Second;
  CSHORT  Milliseconds;
  CSHORT  Weekday;
} TIME_FIELDS, *PTIME_FIELDS;

typedef PVOID 
(DDKAPI *PALLOCATE_FUNCTION)(
  /*IN*/ POOL_TYPE  PoolType,
  /*IN*/ SIZE_T  NumberOfBytes,
  /*IN*/ ULONG  Tag);

typedef VOID 
(DDKAPI *PFREE_FUNCTION)(
  /*IN*/ PVOID  Buffer);

#define GENERAL_LOOKASIDE_S \
  SLIST_HEADER  ListHead; \
  USHORT  Depth; \
  USHORT  MaximumDepth; \
  ULONG  TotalAllocates; \
  _ANONYMOUS_UNION union { \
    ULONG  AllocateMisses; \
    ULONG  AllocateHits; \
  } DUMMYUNIONNAME; \
  ULONG  TotalFrees; \
  _ANONYMOUS_UNION union { \
    ULONG  FreeMisses; \
    ULONG  FreeHits; \
  } DUMMYUNIONNAME2; \
  POOL_TYPE  Type; \
  ULONG  Tag; \
  ULONG  Size; \
  PALLOCATE_FUNCTION  Allocate; \
  PFREE_FUNCTION  Free; \
  LIST_ENTRY  ListEntry; \
  ULONG  LastTotalAllocates; \
  _ANONYMOUS_UNION union { \
    ULONG  LastAllocateMisses; \
    ULONG  LastAllocateHits; \
  } DUMMYUNIONNAME3; \
  ULONG Future[2];

typedef struct _GENERAL_LOOKASIDE {
  GENERAL_LOOKASIDE_S
} GENERAL_LOOKASIDE, *PGENERAL_LOOKASIDE;

typedef struct _NPAGED_LOOKASIDE_LIST {
  GENERAL_LOOKASIDE_S
  KSPIN_LOCK  Obsoleted;
} NPAGED_LOOKASIDE_LIST, *PNPAGED_LOOKASIDE_LIST;

typedef struct _PAGED_LOOKASIDE_LIST {
  GENERAL_LOOKASIDE_S
  FAST_MUTEX  Obsoleted;
} PAGED_LOOKASIDE_LIST, *PPAGED_LOOKASIDE_LIST;

typedef struct _CALLBACK_OBJECT *PCALLBACK_OBJECT;

typedef VOID  (DDKAPI *PCALLBACK_FUNCTION)(
  /*IN*/ PVOID  CallbackContext,
  /*IN*/ PVOID  Argument1,
  /*IN*/ PVOID  Argument2);

typedef enum _EVENT_TYPE {
  NotificationEvent,
  SynchronizationEvent
} EVENT_TYPE;

typedef enum _KWAIT_REASON {
  Executive,
  FreePage,
  PageIn,
  PoolAllocation,
  DelayExecution,
  Suspended,
  UserRequest,
  WrExecutive,
  WrFreePage,
  WrPageIn,
  WrPoolAllocation,
  WrDelayExecution,
  WrSuspended,
  WrUserRequest,
  WrEventPair,
  WrQueue,
  WrLpcReceive,
  WrLpcReply,
  WrVirtualMemory,
  WrPageOut,
  WrRendezvous,
  Spare2,
  Spare3,
  Spare4,
  Spare5,
  Spare6,
  WrKernel,
  MaximumWaitReason
} KWAIT_REASON;

typedef struct _KWAIT_BLOCK {
  LIST_ENTRY  WaitListEntry;
  struct _KTHREAD * RESTRICTED_POINTER  Thread;
  PVOID  Object;
  struct _KWAIT_BLOCK * RESTRICTED_POINTER  NextWaitBlock;
  USHORT  WaitKey;
  USHORT  WaitType;
} KWAIT_BLOCK, *PKWAIT_BLOCK, *RESTRICTED_POINTER PRKWAIT_BLOCK;

typedef struct _IO_REMOVE_LOCK_TRACKING_BLOCK * PIO_REMOVE_LOCK_TRACKING_BLOCK;

typedef struct _IO_REMOVE_LOCK_COMMON_BLOCK {
  BOOLEAN  Removed;
  BOOLEAN  Reserved[3];
  LONG  IoCount;
  KEVENT  RemoveEvent;
} IO_REMOVE_LOCK_COMMON_BLOCK;

typedef struct _IO_REMOVE_LOCK_DBG_BLOCK {
  LONG  Signature;
  LONG  HighWatermark;
  LONGLONG  MaxLockedTicks;
  LONG  AllocateTag;
  LIST_ENTRY  LockList;
  KSPIN_LOCK  Spin;
  LONG  LowMemoryCount;
  ULONG  Reserved1[4];
  PVOID  Reserved2;
  PIO_REMOVE_LOCK_TRACKING_BLOCK  Blocks;
} IO_REMOVE_LOCK_DBG_BLOCK;

typedef struct _IO_REMOVE_LOCK {
  IO_REMOVE_LOCK_COMMON_BLOCK  Common;
#ifdef DBG
  IO_REMOVE_LOCK_DBG_BLOCK  Dbg;
#endif
} IO_REMOVE_LOCK, *PIO_REMOVE_LOCK;

typedef struct _IO_WORKITEM *PIO_WORKITEM;

typedef VOID 
(DDKAPI *PIO_WORKITEM_ROUTINE)(
  /*IN*/ PDEVICE_OBJECT  DeviceObject,
  /*IN*/ PVOID  Context);

typedef struct _SHARE_ACCESS {
  ULONG  OpenCount;
  ULONG  Readers;
  ULONG  Writers;
  ULONG  Deleters;
  ULONG  SharedRead;
  ULONG  SharedWrite;
  ULONG  SharedDelete;
} SHARE_ACCESS, *PSHARE_ACCESS;

typedef enum _KINTERRUPT_MODE {
  LevelSensitive,
  Latched
} KINTERRUPT_MODE;

typedef VOID 
(DDKAPI *PKINTERRUPT_ROUTINE)(
  VOID);

typedef enum _KPROFILE_SOURCE {
  ProfileTime,
  ProfileAlignmentFixup,
  ProfileTotalIssues,
  ProfilePipelineDry,
  ProfileLoadInstructions,
  ProfilePipelineFrozen,
  ProfileBranchInstructions,
  ProfileTotalNonissues,
  ProfileDcacheMisses,
  ProfileIcacheMisses,
  ProfileCacheMisses,
  ProfileBranchMispredictions,
  ProfileStoreInstructions,
  ProfileFpInstructions,
  ProfileIntegerInstructions,
  Profile2Issue,
  Profile3Issue,
  Profile4Issue,
  ProfileSpecialInstructions,
  ProfileTotalCycles,
  ProfileIcacheIssues,
  ProfileDcacheAccesses,
  ProfileMemoryBarrierCycles,
  ProfileLoadLinkedIssues,
  ProfileMaximum
} KPROFILE_SOURCE;

typedef enum _CREATE_FILE_TYPE {
  CreateFileTypeNone,
  CreateFileTypeNamedPipe,
  CreateFileTypeMailslot
} CREATE_FILE_TYPE;

typedef struct _CONFIGURATION_INFORMATION {
  ULONG  DiskCount;
  ULONG  FloppyCount;
  ULONG  CdRomCount;
  ULONG  TapeCount;
  ULONG  ScsiPortCount;
  ULONG  SerialCount;
  ULONG  ParallelCount;
  BOOLEAN  AtDiskPrimaryAddressClaimed;
  BOOLEAN  AtDiskSecondaryAddressClaimed;
  ULONG  Version;
  ULONG  MediumChangerCount;
} CONFIGURATION_INFORMATION, *PCONFIGURATION_INFORMATION;

typedef enum _CONFIGURATION_TYPE {
  ArcSystem,
  CentralProcessor,
  FloatingPointProcessor,
  PrimaryIcache,
  PrimaryDcache,
  SecondaryIcache,
  SecondaryDcache,
  SecondaryCache,
  EisaAdapter,
  TcAdapter,
  ScsiAdapter,
  DtiAdapter,
  MultiFunctionAdapter,
  DiskController,
  TapeController,
  CdromController,
  WormController,
  SerialController,
  NetworkController,
  DisplayController,
  ParallelController,
  PointerController,
  KeyboardController,
  AudioController,
  OtherController,
  DiskPeripheral,
  FloppyDiskPeripheral,
  TapePeripheral,
  ModemPeripheral,
  MonitorPeripheral,
  PrinterPeripheral,
  PointerPeripheral,
  KeyboardPeripheral,
  TerminalPeripheral,
  OtherPeripheral,
  LinePeripheral,
  NetworkPeripheral,
  SystemMemory,
  DockingInformation,
  RealModeIrqRoutingTable,
  MaximumType
} CONFIGURATION_TYPE, *PCONFIGURATION_TYPE;

typedef NTSTATUS (*PIO_QUERY_DEVICE_ROUTINE)(
  /*IN*/ PVOID  Context,
  /*IN*/ PUNICODE_STRING  PathName,
  /*IN*/ INTERFACE_TYPE  BusType,
  /*IN*/ ULONG  BusNumber,
  /*IN*/ PKEY_VALUE_FULL_INFORMATION  *BusInformation,
  /*IN*/ CONFIGURATION_TYPE  ControllerType,
  /*IN*/ ULONG  ControllerNumber,
  /*IN*/ PKEY_VALUE_FULL_INFORMATION  *ControllerInformation,
  /*IN*/ CONFIGURATION_TYPE  PeripheralType,
  /*IN*/ ULONG  PeripheralNumber,
  /*IN*/ PKEY_VALUE_FULL_INFORMATION  *PeripheralInformation);

typedef enum _WORK_QUEUE_TYPE {
  CriticalWorkQueue,
  DelayedWorkQueue,
  HyperCriticalWorkQueue,
  MaximumWorkQueue
} WORK_QUEUE_TYPE;

typedef VOID 
(DDKAPI *PWORKER_THREAD_ROUTINE)(
  /*IN*/ PVOID Parameter);

typedef struct _WORK_QUEUE_ITEM {
  LIST_ENTRY  List;
  PWORKER_THREAD_ROUTINE  WorkerRoutine;
  PVOID  Parameter;
} WORK_QUEUE_ITEM, *PWORK_QUEUE_ITEM;

typedef enum _KBUGCHECK_BUFFER_DUMP_STATE {
    BufferEmpty,
    BufferInserted,
    BufferStarted,
    BufferFinished,
    BufferIncomplete
} KBUGCHECK_BUFFER_DUMP_STATE;

typedef VOID 
(DDKAPI *PKBUGCHECK_CALLBACK_ROUTINE)(
  /*IN*/ PVOID  Buffer,
  /*IN*/ ULONG  Length);

typedef struct _KBUGCHECK_CALLBACK_RECORD {
  LIST_ENTRY  Entry;
  PKBUGCHECK_CALLBACK_ROUTINE  CallbackRoutine;
  PVOID  Buffer;
  ULONG  Length;
  PUCHAR  Component;
  ULONG_PTR  Checksum;
  UCHAR  State;
} KBUGCHECK_CALLBACK_RECORD, *PKBUGCHECK_CALLBACK_RECORD;

/*
 * VOID
 * KeInitializeCallbackRecord(
 * IN PKBUGCHECK_CALLBACK_RECORD  CallbackRecord)
 */
#define KeInitializeCallbackRecord(CallbackRecord) \
  CallbackRecord->State = BufferEmpty;

typedef enum _KDPC_IMPORTANCE {
  LowImportance,
  MediumImportance,
  HighImportance
} KDPC_IMPORTANCE;

typedef enum _MEMORY_CACHING_TYPE_ORIG {
  MmFrameBufferCached = 2
} MEMORY_CACHING_TYPE_ORIG;

typedef enum _MEMORY_CACHING_TYPE {
  MmNonCached = FALSE,
  MmCached = TRUE,
  MmWriteCombined = MmFrameBufferCached,
  MmHardwareCoherentCached,
  MmNonCachedUnordered,
  MmUSWCCached,
  MmMaximumCacheType
} MEMORY_CACHING_TYPE;

typedef enum _MM_PAGE_PRIORITY {
  LowPagePriority,
  NormalPagePriority = 16,
  HighPagePriority = 32
} MM_PAGE_PRIORITY;

typedef enum _LOCK_OPERATION {
  IoReadAccess,
  IoWriteAccess,
  IoModifyAccess
} LOCK_OPERATION;

typedef enum _MM_SYSTEM_SIZE {
  MmSmallSystem,
  MmMediumSystem,
  MmLargeSystem
} MM_SYSTEM_SIZE;

typedef struct _OBJECT_HANDLE_INFORMATION {
  ULONG HandleAttributes;
  ACCESS_MASK GrantedAccess;
} OBJECT_HANDLE_INFORMATION, *POBJECT_HANDLE_INFORMATION;

typedef struct _CLIENT_ID {
  HANDLE  UniqueProcess;
  HANDLE  UniqueThread;
} CLIENT_ID, *PCLIENT_ID;

typedef VOID 
(DDKAPI *PKSTART_ROUTINE)(
  /*IN*/ PVOID  StartContext);

typedef VOID 
(DDKAPI *PCREATE_PROCESS_NOTIFY_ROUTINE)(
  /*IN*/ HANDLE  ParentId,
  /*IN*/ HANDLE  ProcessId,
  /*IN*/ BOOLEAN  Create);

typedef VOID 
(DDKAPI *PCREATE_THREAD_NOTIFY_ROUTINE)(
  /*IN*/ HANDLE  ProcessId,
  /*IN*/ HANDLE  ThreadId,
  /*IN*/ BOOLEAN  Create);

typedef struct _IMAGE_INFO {
  _ANONYMOUS_UNION union {
    ULONG  Properties;
    _ANONYMOUS_STRUCT struct {
      ULONG  ImageAddressingMode  : 8;
      ULONG  SystemModeImage      : 1;
      ULONG  ImageMappedToAllPids : 1;
      ULONG  Reserved             : 22;
    } DUMMYSTRUCTNAME;
  } DUMMYUNIONNAME;
  PVOID  ImageBase;
  ULONG  ImageSelector;
  SIZE_T  ImageSize;
  ULONG  ImageSectionNumber;
} IMAGE_INFO, *PIMAGE_INFO;

#define IMAGE_ADDRESSING_MODE_32BIT       3

typedef VOID 
(DDKAPI *PLOAD_IMAGE_NOTIFY_ROUTINE)(
  /*IN*/ PUNICODE_STRING  FullImageName,
  /*IN*/ HANDLE  ProcessId,
  /*IN*/ PIMAGE_INFO  ImageInfo);

typedef enum _PROCESSINFOCLASS {
  ProcessBasicInformation,
  ProcessQuotaLimits,
  ProcessIoCounters,
  ProcessVmCounters,
  ProcessTimes,
  ProcessBasePriority,
  ProcessRaisePriority,
  ProcessDebugPort,
  ProcessExceptionPort,
  ProcessAccessToken,
  ProcessLdtInformation,
  ProcessLdtSize,
  ProcessDefaultHardErrorMode,
  ProcessIoPortHandlers,
  ProcessPooledUsageAndLimits,
  ProcessWorkingSetWatch,
  ProcessUserModeIOPL,
  ProcessEnableAlignmentFaultFixup,
  ProcessPriorityClass,
  ProcessWx86Information,
  ProcessHandleCount,
  ProcessAffinityMask,
  ProcessPriorityBoost,
  ProcessDeviceMap,
  ProcessSessionInformation,
  ProcessForegroundInformation,
  ProcessWow64Information,
  ProcessImageFileName,
  ProcessLUIDDeviceMapsEnabled,
  ProcessBreakOnTermination,
  ProcessDebugObjectHandle,
  ProcessDebugFlags,
  ProcessHandleTracing,
  MaxProcessInfoClass
} PROCESSINFOCLASS;

typedef enum _THREADINFOCLASS {
  ThreadBasicInformation,
  ThreadTimes,
  ThreadPriority,
  ThreadBasePriority,
  ThreadAffinityMask,
  ThreadImpersonationToken,
  ThreadDescriptorTableEntry,
  ThreadEnableAlignmentFaultFixup,
  ThreadEventPair_Reusable,
  ThreadQuerySetWin32StartAddress,
  ThreadZeroTlsCell,
  ThreadPerformanceCount,
  ThreadAmILastThread,
  ThreadIdealProcessor,
  ThreadPriorityBoost,
  ThreadSetTlsArrayAddress,
  ThreadIsIoPending,
  ThreadHideFromDebugger,
  ThreadBreakOnTermination,
  MaxThreadInfoClass
} THREADINFOCLASS;

//#define ES_SYSTEM_REQUIRED                0x00000001
//#define ES_DISPLAY_REQUIRED               0x00000002
//#define ES_USER_PRESENT                   0x00000004
//#define ES_CONTINUOUS                     0x80000000

typedef ULONG EXECUTION_STATE;

typedef VOID 
(DDKAPI *PREQUEST_POWER_COMPLETE)(
  /*IN*/ PDEVICE_OBJECT  DeviceObject,
  /*IN*/ UCHAR  MinorFunction,
  /*IN*/ POWER_STATE  PowerState,
  /*IN*/ PVOID  Context,
  /*IN*/ PIO_STATUS_BLOCK  IoStatus);

typedef enum _TRACE_INFORMATION_CLASS {
  TraceIdClass,
  TraceHandleClass,
  TraceEnableFlagsClass,
  TraceEnableLevelClass,
  GlobalLoggerHandleClass,
  EventLoggerHandleClass,
  AllLoggerHandlesClass,
  TraceHandleByNameClass
} TRACE_INFORMATION_CLASS;

typedef NTSTATUS 
(DDKAPI *PEX_CALLBACK_FUNCTION)(
  /*IN*/ PVOID  CallbackContext,
  /*IN*/ PVOID  Argument1,
  /*IN*/ PVOID  Argument2);



/*
** Storage structures

typedef enum _PARTITION_STYLE {
  PARTITION_STYLE_MBR,
  PARTITION_STYLE_GPT
} PARTITION_STYLE;
typedef struct _CREATE_DISK_MBR {
  ULONG  Signature;
} CREATE_DISK_MBR, *PCREATE_DISK_MBR;


typedef struct _CREATE_DISK_GPT {
  GUID  DiskId;
  ULONG  MaxPartitionCount;
} CREATE_DISK_GPT, *PCREATE_DISK_GPT;

typedef struct _CREATE_DISK {
  PARTITION_STYLE  PartitionStyle;
  _ANONYMOUS_UNION union {
    CREATE_DISK_MBR  Mbr;
    CREATE_DISK_GPT  Gpt;
  } DUMMYUNIONNAME;
} CREATE_DISK, *PCREATE_DISK;
*/
typedef struct _DISK_SIGNATURE {
  ULONG  PartitionStyle;
  _ANONYMOUS_UNION union {
    struct {
      ULONG  Signature;
      ULONG  CheckSum;
    } Mbr;
    struct {
      GUID  DiskId;
    } Gpt;
  } DUMMYUNIONNAME;
} DISK_SIGNATURE, *PDISK_SIGNATURE;

typedef VOID 
(DDKFASTAPI *PTIME_UPDATE_NOTIFY_ROUTINE)(
  /*IN*/ HANDLE  ThreadId,
  /*IN*/ KPROCESSOR_MODE  Mode);

#define DBG_STATUS_CONTROL_C              1
#define DBG_STATUS_SYSRQ                  2
#define DBG_STATUS_BUGCHECK_FIRST         3
#define DBG_STATUS_BUGCHECK_SECOND        4
#define DBG_STATUS_FATAL                  5
#define DBG_STATUS_DEBUG_CONTROL          6
#define DBG_STATUS_WORKER                 7

typedef struct _PHYSICAL_MEMORY_RANGE {
  PHYSICAL_ADDRESS  BaseAddress;
  LARGE_INTEGER  NumberOfBytes;
} PHYSICAL_MEMORY_RANGE, *PPHYSICAL_MEMORY_RANGE;

typedef ULONG_PTR
(*PDRIVER_VERIFIER_THUNK_ROUTINE)(
  /*IN*/ PVOID  Context);

typedef struct _DRIVER_VERIFIER_THUNK_PAIRS {
  PDRIVER_VERIFIER_THUNK_ROUTINE  PristineRoutine;
  PDRIVER_VERIFIER_THUNK_ROUTINE  NewRoutine;
} DRIVER_VERIFIER_THUNK_PAIRS, *PDRIVER_VERIFIER_THUNK_PAIRS;

#define DRIVER_VERIFIER_SPECIAL_POOLING             0x0001
#define DRIVER_VERIFIER_FORCE_IRQL_CHECKING         0x0002
#define DRIVER_VERIFIER_INJECT_ALLOCATION_FAILURES  0x0004
#define DRIVER_VERIFIER_TRACK_POOL_ALLOCATIONS      0x0008
#define DRIVER_VERIFIER_IO_CHECKING                 0x0010

#define RTL_RANGE_LIST_ADD_IF_CONFLICT    0x00000001
#define RTL_RANGE_LIST_ADD_SHARED         0x00000002

#define RTL_RANGE_LIST_SHARED_OK          0x00000001
#define RTL_RANGE_LIST_NULL_CONFLICT_OK   0x00000002

#define RTL_RANGE_LIST_SHARED_OK          0x00000001
#define RTL_RANGE_LIST_NULL_CONFLICT_OK   0x00000002

#define RTL_RANGE_LIST_MERGE_IF_CONFLICT  RTL_RANGE_LIST_ADD_IF_CONFLICT

typedef struct _RTL_RANGE {
  ULONGLONG  Start;
  ULONGLONG  End;
  PVOID  UserData;
  PVOID  Owner;
  UCHAR  Attributes;
  UCHAR  Flags;
} RTL_RANGE, *PRTL_RANGE;

#define RTL_RANGE_SHARED                  0x01
#define RTL_RANGE_CONFLICT                0x02

typedef struct _RTL_RANGE_LIST {
  LIST_ENTRY  ListHead;
  ULONG  Flags;
  ULONG  Count;
  ULONG  Stamp;
} RTL_RANGE_LIST, *PRTL_RANGE_LIST;

typedef struct _RANGE_LIST_ITERATOR {
  PLIST_ENTRY  RangeListHead;
  PLIST_ENTRY  MergedHead;
  PVOID  Current;
  ULONG  Stamp;
} RTL_RANGE_LIST_ITERATOR, *PRTL_RANGE_LIST_ITERATOR;

typedef BOOLEAN
(*PRTL_CONFLICT_RANGE_CALLBACK)(
  /*IN*/ PVOID  Context,
  /*IN*/ PRTL_RANGE  Range);

#define HASH_STRING_ALGORITHM_DEFAULT     0
#define HASH_STRING_ALGORITHM_X65599      1
#define HASH_STRING_ALGORITHM_INVALID     0xffffffff

typedef enum _SUITE_TYPE {
  SmallBusiness,
  Enterprise,
  BackOffice,
  CommunicationServer,
  TerminalServer,
  SmallBusinessRestricted,
  EmbeddedNT,
  DataCenter,
  SingleUserTS,
  Personal,
  Blade,
  MaxSuiteType
} SUITE_TYPE;

typedef VOID 
(DDKAPI *PTIMER_APC_ROUTINE)(
  /*IN*/ PVOID  TimerContext,
  /*IN*/ ULONG  TimerLowValue,
  /*IN*/ LONG  TimerHighValue);



/*
** WMI structures
*/

typedef VOID 
(DDKAPI *WMI_NOTIFICATION_CALLBACK)(
  PVOID  Wnode,
  PVOID  Context);


/*
** Architecture specific structures
*/

#ifdef _X86_

typedef ULONG PFN_NUMBER, *PPFN_NUMBER;

#define PASSIVE_LEVEL                      0
#define LOW_LEVEL                          0
#define APC_LEVEL                          1
#define DISPATCH_LEVEL                     2
#define SYNCH_LEVEL                       27
#define PROFILE_LEVEL                     27
#define CLOCK1_LEVEL                      28
#define CLOCK2_LEVEL                      28
#define IPI_LEVEL                         29
#define POWER_LEVEL                       30
#define HIGH_LEVEL                        31

typedef struct _KPCR_TIB {
  PVOID  ExceptionList;         /* 00 */
  PVOID  StackBase;             /* 04 */
  PVOID  StackLimit;            /* 08 */
  PVOID  SubSystemTib;          /* 0C */
  _ANONYMOUS_UNION union {
    PVOID  FiberData;           /* 10 */
    DWORD  Version;             /* 10 */
  } DUMMYUNIONNAME;
  PVOID  ArbitraryUserPointer;  /* 14 */
  struct _NT_TIB *Self;         /* 18 */
} KPCR_TIB, *PKPCR_TIB;         /* 1C */

#define PCR_MINOR_VERSION 1
#define PCR_MAJOR_VERSION 1

typedef struct _KPCR {
  KPCR_TIB  Tib;                /* 00 */
  struct _KPCR  *Self;          /* 1C */
  struct _KPRCB  *PCRCB;        /* 20 */
  KIRQL  Irql;                  /* 24 */
  ULONG  IRR;                   /* 28 */
  ULONG  IrrActive;             /* 2C */
  ULONG  IDR;                   /* 30 */
  PVOID  KdVersionBlock;        /* 34 */
  PUSHORT  IDT;                 /* 38 */
  PUSHORT  GDT;                 /* 3C */
  struct _KTSS  *TSS;           /* 40 */
  USHORT  MajorVersion;         /* 44 */
  USHORT  MinorVersion;         /* 46 */
  KAFFINITY  SetMember;         /* 48 */
  ULONG  StallScaleFactor;      /* 4C */
  UCHAR  SpareUnused;           /* 50 */
  UCHAR  Number;                /* 51 */
} KPCR, *PKPCR;                 /* 54 */

typedef struct _KFLOATING_SAVE {
  ULONG  ControlWord;
  ULONG  StatusWord;
  ULONG  ErrorOffset;
  ULONG  ErrorSelector;
  ULONG  DataOffset;
  ULONG  DataSelector;
  ULONG  Cr0NpxState;
  ULONG  Spare1;
} KFLOATING_SAVE, *PKFLOATING_SAVE;

#define PAGE_SIZE                         0x1000
#define PAGE_SHIFT                        12L

extern NTOSAPI PVOID *MmHighestUserAddress;
extern NTOSAPI PVOID *MmSystemRangeStart;
extern NTOSAPI ULONG *MmUserProbeAddress;

#define MM_HIGHEST_USER_ADDRESS           *MmHighestUserAddress
#define MM_SYSTEM_RANGE_START             *MmSystemRangeStart
#define MM_USER_PROBE_ADDRESS             *MmUserProbeAddress
#define MM_LOWEST_USER_ADDRESS            (PVOID)0x10000
#define MM_LOWEST_SYSTEM_ADDRESS          (PVOID)0xC0C00000

#define KI_USER_SHARED_DATA               0xffdf0000
#define SharedUserData                    ((KUSER_SHARED_DATA * CONST) KI_USER_SHARED_DATA)

#define EFLAG_SIGN                        0x8000
#define EFLAG_ZERO                        0x4000
#define EFLAG_SELECT                      (EFLAG_SIGN | EFLAG_ZERO)

#define RESULT_NEGATIVE                   ((EFLAG_SIGN & ~EFLAG_ZERO) & EFLAG_SELECT)
#define RESULT_ZERO                       ((~EFLAG_SIGN & EFLAG_ZERO) & EFLAG_SELECT)
#define RESULT_POSITIVE                   ((~EFLAG_SIGN & ~EFLAG_ZERO) & EFLAG_SELECT)

typedef enum _INTERLOCKED_RESULT {
  ResultNegative = RESULT_NEGATIVE,
  ResultZero = RESULT_ZERO,
  ResultPositive = RESULT_POSITIVE
} INTERLOCKED_RESULT;

NTOSAPI
KIRQL
DDKAPI
KeGetCurrentIrql(
  VOID);

/*
 * ULONG
 * KeGetCurrentProcessorNumber(
 *   VOID)
 */
#define KeGetCurrentProcessorNumber() \
  ((ULONG)KeGetCurrentKPCR()->Number)


#if  __USE_NTOSKRNL__
/* CAREFUL: These are exported from ntoskrnl.exe as __fastcall functions,
   but are also exported from kernel32.dll and declared in winbase.h as
   __stdcall */
#if !defined(__INTERLOCKED_DECLARED)
#define __INTERLOCKED_DECLARED


#endif /* !__INTERLOCKED_DECLARED */
#endif /*  __USE_NTOSKRNL__ */

NTOSAPI
VOID
DDKFASTAPI
KefAcquireSpinLockAtDpcLevel(
  /*IN*/ PKSPIN_LOCK  SpinLock);

NTOSAPI
VOID
DDKFASTAPI
KefReleaseSpinLockFromDpcLevel(
  /*IN*/ PKSPIN_LOCK  SpinLock);

#define KeAcquireSpinLockAtDpcLevel(SpinLock) KefAcquireSpinLockAtDpcLevel(SpinLock)
#define KeReleaseSpinLockFromDpcLevel(SpinLock) KefReleaseSpinLockFromDpcLevel(SpinLock)

#define RtlCopyMemoryNonTemporal RtlCopyMemory

#define KeGetDcacheFillSize() 1L

#endif /* _X86_ */



/*
** Utillity functions
*/

#define ARGUMENT_PRESENT(ArgumentPointer) \
  ((BOOLEAN) ((PVOID)ArgumentPointer != (PVOID)NULL))

/*
 * ULONG
 * BYTE_OFFSET(
 * IN PVOID  Va)
 */
#define BYTE_OFFSET(Va) \
  ((ULONG) ((ULONG_PTR) (Va) & (PAGE_SIZE - 1)))

/*
 * ULONG
 * BYTES_TO_PAGES(
 * IN ULONG  Size)
 */
#define BYTES_TO_PAGES(Size) \
  ((ULONG) ((ULONG_PTR) (Size) >> PAGE_SHIFT) + (((ULONG) (Size) & (PAGE_SIZE - 1)) != 0))

/*
 * PCHAR
 * CONTAINING_RECORD(
 * IN PCHAR  Address,
 * IN TYPE  Type,
 * IN PCHAR  Field);
 */
#ifndef CONTAINING_RECORD
#define CONTAINING_RECORD(Address, Type, Field) \
  ((Type *) (((ULONG_PTR) Address) - FIELD_OFFSET(Type, Field)))
#endif

/* LONG
 * FIELD_OFFSET(
 * IN TYPE  Type,
 * IN PCHAR  Field);
 */
#ifndef FIELD_OFFSET
#define FIELD_OFFSET(Type, Field) \
  ((LONG) (&(((Type *) 0)->Field)))
#endif

/*
 * PVOID
 * PAGE_ALIGN(
 * IN PVOID  Va)
 */
#define PAGE_ALIGN(Va) \
  ((PVOID) ((ULONG_PTR)(Va) & ~(PAGE_SIZE - 1)))

/*
 * ULONG_PTR
 * ROUND_TO_PAGES(
 * IN ULONG_PTR  Size)
 */
#define ROUND_TO_PAGES(Size) \
  ((ULONG_PTR) (((ULONG_PTR) Size + PAGE_SIZE - 1) & ~(PAGE_SIZE - 1)))

NTOSAPI
VOID
DDKAPI
RtlAssert(
  /*IN*/ PVOID  FailedAssertion,
  /*IN*/ PVOID  FileName,
  /*IN*/ ULONG  LineNumber,
  /*IN*/ PCHAR  Message);

#ifdef DBG

#define ASSERT(exp) \
  ((!(exp)) ? \
    (RtlAssert( #exp, __FILE__, __LINE__, NULL ), FALSE) : TRUE)

#define ASSERTMSG(msg, exp) \
  ((!(exp)) ? \
    (RtlAssert( #exp, __FILE__, __LINE__, msg ), FALSE) : TRUE)

#define RTL_SOFT_ASSERT(exp) \
  ((!(_exp)) ? \
    (DbgPrint("%s(%d): Soft assertion failed\n   Expression: %s\n", __FILE__, __LINE__, #exp), FALSE) : TRUE)

#define RTL_SOFT_ASSERTMSG(msg, exp) \
  ((!(exp)) ? \
    (DbgPrint("%s(%d): Soft assertion failed\n   Expression: %s\n   Message: %s\n", __FILE__, __LINE__, #exp, (msg)), FALSE) : TRUE)

#define RTL_VERIFY(exp) ASSERT(exp)
#define RTL_VERIFYMSG(msg, exp) ASSERT(msg, exp)

#define RTL_SOFT_VERIFY(exp) RTL_SOFT_ASSERT(exp)
#define RTL_SOFT_VERIFYMSG(msg, exp) RTL_SOFT_ASSERTMSG(msg, exp)

#else /* !DBG */

#define ASSERT(exp) ((VOID) 0)
#define ASSERTMSG(msg, exp) ((VOID) 0)

#define RTL_SOFT_ASSERT(exp) ((VOID) 0)
#define RTL_SOFT_ASSERTMSG(msg, exp) ((VOID) 0)

#define RTL_VERIFY(exp) ((exp) ? TRUE : FALSE)
#define RTL_VERIFYMSG(msg, exp) ((exp) ? TRUE : FALSE)

#define RTL_SOFT_VERIFY(exp) ((exp) ? TRUE : FALSE)
#define RTL_SOFT_VERIFYMSG(msg, exp) ((exp) ? TRUE : FALSE)

#endif /* DBG */


/*
** Driver support routines
*/

/** Runtime library routines **/

/*
 * VOID
 * InitializeListHead(
 * IN PLIST_ENTRY  ListHead)
 */
#define InitializeListHead(_ListHead) \
{ \
  (_ListHead)->Flink = (_ListHead); \
  (_ListHead)->Blink = (_ListHead); \
}

/*
 * VOID
 * InsertHeadList(
 * IN PLIST_ENTRY  ListHead,
 * IN PLIST_ENTRY  Entry)
 */
#define InsertHeadList(_ListHead, \
                       _Entry) \
{ \
  PLIST_ENTRY _OldFlink; \
  _OldFlink = (_ListHead)->Flink; \
  (_Entry)->Flink = _OldFlink; \
  (_Entry)->Blink = (_ListHead); \
  _OldFlink->Blink = (_Entry); \
  (_ListHead)->Flink = (_Entry); \
}

/*
 * VOID
 * InsertTailList(
 * IN PLIST_ENTRY  ListHead,
 * IN PLIST_ENTRY  Entry)
 */
#define InsertTailList(_ListHead, \
                       _Entry) \
{ \
	PLIST_ENTRY _OldBlink; \
	_OldBlink = (_ListHead)->Blink; \
	(_Entry)->Flink = (_ListHead); \
	(_Entry)->Blink = _OldBlink; \
	_OldBlink->Flink = (_Entry); \
	(_ListHead)->Blink = (_Entry); \
}

/*
 * BOOLEAN
 * IsListEmpty(
 * IN PLIST_ENTRY  ListHead)
 */
#define IsListEmpty(_ListHead) \
  ((_ListHead)->Flink == (_ListHead))

static __inline PSINGLE_LIST_ENTRY 
PopEntryList(
  /*IN*/ PSINGLE_LIST_ENTRY  ListHead)
{
	PSINGLE_LIST_ENTRY Entry;

	Entry = ListHead->Next;
	if (Entry != NULL)
	{
		ListHead->Next = Entry->Next;
	}
  return Entry;
}

/*
 * VOID
 * PushEntryList(
 * IN PSINGLE_LIST_ENTRY  ListHead,
 * IN PSINGLE_LIST_ENTRY  Entry)
 */
#define PushEntryList(_ListHead, \
                      _Entry) \
{ \
	(_Entry)->Next = (_ListHead)->Next; \
	(_ListHead)->Next = (_Entry); \
}

/*
 * VOID
 * RemoveEntryList(
 * IN PLIST_ENTRY  Entry)
 */
#define RemoveEntryList(_Entry) \
{ \
	PLIST_ENTRY _OldFlink; \
	PLIST_ENTRY _OldBlink; \
	_OldFlink = (_Entry)->Flink; \
	_OldBlink = (_Entry)->Blink; \
	_OldFlink->Blink = _OldBlink; \
	_OldBlink->Flink = _OldFlink; \
  (_Entry)->Flink = NULL; \
  (_Entry)->Blink = NULL; \
}

static __inline PLIST_ENTRY 
RemoveHeadList(
  /*IN*/ PLIST_ENTRY  ListHead)
{
	PLIST_ENTRY OldFlink;
	PLIST_ENTRY OldBlink;
	PLIST_ENTRY Entry;

	Entry = ListHead->Flink;
	OldFlink = ListHead->Flink->Flink;
	OldBlink = ListHead->Flink->Blink;
	OldFlink->Blink = OldBlink;
	OldBlink->Flink = OldFlink;

  if (Entry != ListHead)
  {
    Entry->Flink = NULL;
    Entry->Blink = NULL;
  }

	return Entry;
}

static __inline PLIST_ENTRY
RemoveTailList(
  /*IN*/ PLIST_ENTRY  ListHead)
{
	PLIST_ENTRY OldFlink;
	PLIST_ENTRY OldBlink;
	PLIST_ENTRY Entry;

	Entry = ListHead->Blink;
	OldFlink = ListHead->Blink->Flink;
	OldBlink = ListHead->Blink->Blink;
	OldFlink->Blink = OldBlink;
	OldBlink->Flink = OldFlink;

  if (Entry != ListHead)
  {
    Entry->Flink = NULL;
    Entry->Blink = NULL;
  }
   
  return Entry;
}

/*
 * USHORT
 * QueryDepthSList(
 * IN PSLIST_HEADER  SListHead)
 */
#define QueryDepthSList(_SListHead) \
  ((USHORT) ((_SListHead)->Alignment & 0xffff))

#define InterlockedFlushSList(ListHead) ExInterlockedFlushSList(ListHead)

NTOSAPI
ULONG
DDKAPI
RtlAnsiStringToUnicodeSize(
  /*IN*/ PANSI_STRING  AnsiString);

NTOSAPI
NTSTATUS
DDKAPI
RtlAddRange(
  /*IN OUT*/ PRTL_RANGE_LIST  RangeList,
  /*IN*/ ULONGLONG  Start,
  /*IN*/ ULONGLONG  End,
  /*IN*/ UCHAR  Attributes,
  /*IN*/ ULONG  Flags,
  /*IN*/ PVOID  UserData  /*OPTIONAL*/,
  /*IN*/ PVOID  Owner  /*OPTIONAL*/);

NTOSAPI
NTSTATUS
DDKAPI
RtlAnsiStringToUnicodeString(
  /*IN OUT*/ PUNICODE_STRING  DestinationString,
  /*IN*/ PANSI_STRING  SourceString,
  /*IN*/ BOOLEAN  AllocateDestinationString);

NTOSAPI
NTSTATUS
DDKAPI
RtlAppendUnicodeStringToString(
  /*IN OUT*/ PUNICODE_STRING  Destination,
  /*IN*/ PUNICODE_STRING  Source);

NTOSAPI
NTSTATUS
DDKAPI
RtlAppendUnicodeToString(
  /*IN OUT*/ PUNICODE_STRING  Destination,
  /*IN*/ PCWSTR  Source);

NTOSAPI
BOOLEAN
DDKAPI
RtlAreBitsClear(
  /*IN*/ PRTL_BITMAP  BitMapHeader,
  /*IN*/ ULONG  StartingIndex,
  /*IN*/ ULONG  Length); 

NTOSAPI
BOOLEAN
DDKAPI
RtlAreBitsSet(
  /*IN*/ PRTL_BITMAP  BitMapHeader,
  /*IN*/ ULONG  StartingIndex,
  /*IN*/ ULONG  Length); 

NTOSAPI
NTSTATUS
DDKAPI
RtlCharToInteger(
  /*IN*/ PCSZ  String,
  /*IN*/ ULONG  Base  /*OPTIONAL*/,
  /*IN OUT*/ PULONG  Value);

NTOSAPI
ULONG
DDKAPI
RtlCheckBit(
  /*IN*/ PRTL_BITMAP  BitMapHeader,
  /*IN*/ ULONG  BitPosition); 

NTOSAPI
NTSTATUS
DDKAPI
RtlCheckRegistryKey(
  /*IN*/ ULONG  RelativeTo,
  /*IN*/ PWSTR  Path);

NTOSAPI
VOID
DDKAPI
RtlClearAllBits(
  /*IN*/ PRTL_BITMAP  BitMapHeader); 

NTOSAPI
VOID
DDKAPI
RtlClearBit(
  PRTL_BITMAP  BitMapHeader,
  ULONG  BitNumber);

NTOSAPI
VOID
DDKAPI
RtlClearBits(
  /*IN*/ PRTL_BITMAP  BitMapHeader,
  /*IN*/ ULONG  StartingIndex,
  /*IN*/ ULONG  NumberToClear); 

NTOSAPI
SIZE_T
DDKAPI
RtlCompareMemory(
  /*IN*/ CONST VOID  *Source1,
  /*IN*/ CONST VOID  *Source2,
  /*IN*/ SIZE_T  Length);

NTOSAPI
LONG
DDKAPI
RtlCompareString(
  /*IN*/ PSTRING  String1,
  /*IN*/ PSTRING  String2,
  BOOLEAN  CaseInSensitive);

NTOSAPI
LONG
DDKAPI
RtlCompareUnicodeString(
  /*IN*/ PUNICODE_STRING  String1,
  /*IN*/ PUNICODE_STRING  String2,
  /*IN*/ BOOLEAN  CaseInSensitive);

NTOSAPI
LARGE_INTEGER
DDKAPI
RtlConvertLongToLargeInteger(
  /*IN*/ LONG  SignedInteger);

NTOSAPI
LUID
DDKAPI
RtlConvertLongToLuid(
  /*IN*/ LONG  Long);

NTOSAPI
LARGE_INTEGER
DDKAPI
RtlConvertUlongToLargeInteger(
  /*IN*/ ULONG  UnsignedInteger);

NTOSAPI
LUID
DDKAPI
RtlConvertUlongToLuid(
  ULONG  Ulong);

/*
 * VOID
 * RtlCopyMemory(
 * IN VOID UNALIGNED  *Destination,
 * IN CONST VOID UNALIGNED  *Source,
 * IN SIZE_T  Length)
 */
#ifndef RtlCopyMemory
#define RtlCopyMemory(Destination, Source, Length) \
  memcpy(Destination, Source, Length);
#endif

#ifndef RtlCopyBytes
#define RtlCopyBytes RtlCopyMemory
#endif

NTOSAPI
VOID
DDKAPI
RtlCopyMemory32(
  /*IN*/ VOID UNALIGNED  *Destination,
  /*IN*/ CONST VOID UNALIGNED  *Source,
  /*IN*/ ULONG  Length);
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
